Solartraveler/UniversalboxArm/src/apps/11-adc-scope/readme.md

Plots signals of the ADC inputs. Supports trigger and timebase selection.
