Solartraveler/UniversalboxArm/src/apps/10-infrared-decoder/readme.md

Decodes infrared protocols

Shows the last received infrared protocol on the LCD and serial port.

The 1. red LED shows any IR activity.
