Solartraveler/UniversalboxArm/src/apps/08-freertos-helloworld/readme.md

Simple application showing how to run FreeRTOS

Creates 4 Tasks:

1. Letting LED 1 flash

2. Control LED 2 with the input buttons

3. Periodically reset watchdog of the coprocessor

4. Waiting for input on the serial port
