Solartraveler/UniversalboxArm/src/apps/05-coprocessor-control/readme.md

Interacts with the coprocessor over SPI

Use when the AVR coprocessor is programmed with the 05-spi-with-charger firmware.

Allows checking the charging conditions
