Solartraveler/UniversalboxArm/src/apps/04-coprocessor-uart-forward/readme.md

Forwards serial data from the coprocessor

Use when the AVR coprocessor is programmed with the 02-test-everything firmware.

Data from the coprocessor are forwared to the RS232 port.
This avoids connecting a 3.3V to RS232 converter to TP20 of the PCB.

The up key generates a CPU reset.
