Solartraveler/UniversalboxArm/src/apps/01-blinky-hal/readme.md

No key: LEDs count/toggle with 4Hz.

Key control:

Left: 8Hz counting speed

Right: LEDs yellow

Up: LEDs red

Down: LED green
