Solartraveler/UniversalboxArm/src/apps/common/shared-init/stm32l452/main.h

#define KeyUp_Pin GPIO_PIN_13
#define KeyUp_GPIO_Port GPIOC
#define Extern4_Pin GPIO_PIN_0
#define Extern4_GPIO_Port GPIOC
#define Extern3_Pin GPIO_PIN_1
#define Extern3_GPIO_Port GPIOC
#define IrPower_Pin GPIO_PIN_2
#define IrPower_GPIO_Port GPIOC
#define Extern6_Pin GPIO_PIN_3
#define Extern6_GPIO_Port GPIOC
#define Extern14_Pin GPIO_PIN_0
#define Extern14_GPIO_Port GPIOA
#define Extern13_Pin GPIO_PIN_1
#define Extern13_GPIO_Port GPIOA
#define Extern12_Pin GPIO_PIN_2
#define Extern12_GPIO_Port GPIOA
#define Extern11_Pin GPIO_PIN_3
#define Extern11_GPIO_Port GPIOA
#define Extern7_Pin GPIO_PIN_4
#define Extern7_GPIO_Port GPIOA
#define Relay4_Pin GPIO_PIN_5
#define Relay4_GPIO_Port GPIOA
#define Intern4_Pin GPIO_PIN_6
#define Intern4_GPIO_Port GPIOA
#define Intern2_Pin GPIO_PIN_7
#define Intern2_GPIO_Port GPIOA
#define FlashCs_Pin GPIO_PIN_4
#define FlashCs_GPIO_Port GPIOC
#define EspPower_Pin GPIO_PIN_5
#define EspPower_GPIO_Port GPIOC
#define Intern3_Pin GPIO_PIN_0
#define Intern3_GPIO_Port GPIOB
#define Intern1_Pin GPIO_PIN_1
#define Intern1_GPIO_Port GPIOB
#define IrIn_Pin GPIO_PIN_2
#define IrIn_GPIO_Port GPIOB
#define EspRxArmTx_Pin GPIO_PIN_10
#define EspRxArmTx_GPIO_Port GPIOB
#define EspTxArmRx_Pin GPIO_PIN_11
#define EspTxArmRx_GPIO_Port GPIOB
#define Relay2_Pin GPIO_PIN_12
#define Relay2_GPIO_Port GPIOB
#define PerSpiSck_Pin GPIO_PIN_13
#define PerSpiSck_GPIO_Port GPIOB
#define PerSpiMiso_Pin GPIO_PIN_14
#define PerSpiMiso_GPIO_Port GPIOB
#define PerSpiMosi_Pin GPIO_PIN_15
#define PerSpiMosi_GPIO_Port GPIOB
#define Relay3_Pin GPIO_PIN_6
#define Relay3_GPIO_Port GPIOC
#define LcdA0_Pin GPIO_PIN_7
#define LcdA0_GPIO_Port GPIOC
#define KeyDown_Pin GPIO_PIN_8
#define KeyDown_GPIO_Port GPIOC
#define LcdCs_Pin GPIO_PIN_9
#define LcdCs_GPIO_Port GPIOC
#define LcdBacklight_Pin GPIO_PIN_8
#define LcdBacklight_GPIO_Port GPIOA
#define Relay1_Pin GPIO_PIN_9
#define Relay1_GPIO_Port GPIOA
#define PeripheralNPower_Pin GPIO_PIN_10
#define PeripheralNPower_GPIO_Port GPIOA
#define Led2Red_Pin GPIO_PIN_13
#define Led2Red_GPIO_Port GPIOA
#define Led2Green_Pin GPIO_PIN_14
#define Led2Green_GPIO_Port GPIOA
#define KeyLeft_Pin GPIO_PIN_15
#define KeyLeft_GPIO_Port GPIOA
#define AvrSpiSck_Pin GPIO_PIN_10
#define AvrSpiSck_GPIO_Port GPIOC
#define AvrSpiMiso_Pin GPIO_PIN_11
#define AvrSpiMiso_GPIO_Port GPIOC
#define AvrSpiMosi_Pin GPIO_PIN_12
#define AvrSpiMosi_GPIO_Port GPIOC
#define Led1Green_Pin GPIO_PIN_2
#define Led1Green_GPIO_Port GPIOD
#define Extern8_Pin GPIO_PIN_3
#define Extern8_GPIO_Port GPIOB
#define Extern9_Pin GPIO_PIN_4
#define Extern9_GPIO_Port GPIOB
#define Extern10_Pin GPIO_PIN_5
#define Extern10_GPIO_Port GPIOB
#define Rs232Tx_Pin GPIO_PIN_6
#define Rs232Tx_GPIO_Port GPIOB
#define Rs232Rx_Pin GPIO_PIN_7
#define Rs232Rx_GPIO_Port GPIOB
#define Led1Red_Pin GPIO_PIN_8
#define Led1Red_GPIO_Port GPIOB
#define KeyRight_Pin GPIO_PIN_9
#define KeyRight_GPIO_Port GPIOB
