Solartraveler/UniversalboxArm/src/apps/common/shared-init/main.c

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
/* Includes ------------------------------------------------------------------*/
#include "main.h"

/* USER CODE BEGIN Includes */

#include <reent.h>
#include <unistd.h>

#include "appInterface.h"
#include "boxlib/rs232debug.h"


/* USER CODE END Includes */


void SystemClock_Config(void);
/* USER CODE BEGIN 0 */

__attribute__((weak)) void AppCycle(void)
{


}

//See https://stackoverflow.com/questions/73742774/gcc-arm-none-eabi-11-3-is-not-implemented-and-will-always-fail

int _close_r(struct _reent * ptr, int fd) {
	(void)ptr;
	(void)fd;
	return -1;
}

_ssize_t _read_r(struct _reent * ptr, int fd, void *buf, size_t cnt) {
	(void)ptr;
	(void)fd;
	(void)buf;
	(void)cnt;
	return -1;
}

_ssize_t _write_r(struct _reent * ptr, int fd, const void *buf, size_t cnt) {
	(void)ptr;
	(void)fd;
	(void)buf;
	(void)cnt;
	return -1;
}

int _fstat_r(struct _reent * ptr, int fd, struct stat * pstat) {
	(void)ptr;
	(void)fd;
	(void)pstat;
	return -1;
}

off_t _lseek_r(struct _reent * ptr, int fd, off_t pos, int whence) {
	(void)ptr;
	(void)fd;
	(void)pos;
	(void)whence;
	return -1;
}

int _kill_r(struct _reent * ptr, int pid, int sig) {
	(void)ptr;
	(void)pid;
	(void)sig;
	return -1;
}

int _getpid_r(struct _reent * ptr) {
	(void)ptr;
	return -1;
}

int _stat_r(struct _reent * ptr, const char * file, struct stat * pstat) {
	(void)ptr;
	(void)file;
	(void)pstat;
	return -1;
}

int _isatty_r(struct _reent * ptr, int fd) {
	(void)ptr;
	(void)fd;
	return -1;
}

/* USER CODE END 0 */

/**
  * @brief  The application entry point.
  * @retval int
  */
int main(void)
{
  /* MCU Configuration--------------------------------------------------------*/

  /* Reset of all peripherals, Initializes the Flash interface and the Systick. */
  HAL_Init();

  /* Configure the system clock */
  SystemClock_Config();

  /* Initialize all configured peripherals */

  /* USER CODE BEGIN 2 */

  AppInit();

  /* USER CODE END 2 */

  /* Infinite loop */
  /* USER CODE BEGIN WHILE */
  while (1)
  {
    /* USER CODE END WHILE */

    /* USER CODE BEGIN 3 */
    AppCycle();
  }
  /* USER CODE END 3 */
}

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
