Solartraveler/UniversalboxArm/src/common/irmp/irmp.c

/*---------------------------------------------------------------------------------------------------------------------------------------------------
 * irmp.c - infrared multi-protocol decoder, supports several remote control protocols
 *
 * Copyright (c) 2009-2020 Frank Meyer - frank(at)fli4l.de
 *
 * Supported AVR mikrocontrollers:
 *
 * ATtiny87,  ATtiny167
 * ATtiny45,  ATtiny85
 * ATtiny44,  ATtiny84
 * ATmega8,   ATmega16,  ATmega32
 * ATmega162
 * ATmega164, ATmega324, ATmega644,  ATmega644P, ATmega1284, ATmega1284P
 * ATmega88,  ATmega88P, ATmega168,  ATmega168P, ATmega328P
 *
 * This program is free software; you can redistribute it and/or modify
 * it under the terms of the GNU General Public License as published by
 * the Free Software Foundation; either version 2 of the License, or
 * (at your option) any later version.
 *---------------------------------------------------------------------------------------------------------------------------------------------------
 */

#include "irmp.h"

#if IRMP_SUPPORT_GRUNDIG_PROTOCOL == 1 || IRMP_SUPPORT_NOKIA_PROTOCOL == 1 || IRMP_SUPPORT_IR60_PROTOCOL == 1
#  define IRMP_SUPPORT_GRUNDIG_NOKIA_IR60_PROTOCOL  1
#else
#  define IRMP_SUPPORT_GRUNDIG_NOKIA_IR60_PROTOCOL  0
#endif

#if IRMP_SUPPORT_SIEMENS_PROTOCOL == 1 || IRMP_SUPPORT_RUWIDO_PROTOCOL == 1
#  define IRMP_SUPPORT_SIEMENS_OR_RUWIDO_PROTOCOL   1
#else
#  define IRMP_SUPPORT_SIEMENS_OR_RUWIDO_PROTOCOL   0
#endif

#if IRMP_SUPPORT_RC5_PROTOCOL == 1 ||                   \
    IRMP_SUPPORT_RCII_PROTOCOL == 1 ||                  \
    IRMP_SUPPORT_S100_PROTOCOL == 1 ||                  \
    IRMP_SUPPORT_RC6_PROTOCOL == 1 ||                   \
    IRMP_SUPPORT_GRUNDIG_NOKIA_IR60_PROTOCOL == 1 ||    \
    IRMP_SUPPORT_SIEMENS_OR_RUWIDO_PROTOCOL == 1 ||     \
    IRMP_SUPPORT_IR60_PROTOCOL == 1 ||                  \
    IRMP_SUPPORT_A1TVBOX_PROTOCOL == 1 ||               \
    IRMP_SUPPORT_MERLIN_PROTOCOL == 1 ||                \
    IRMP_SUPPORT_ORTEK_PROTOCOL == 1
#  define IRMP_SUPPORT_MANCHESTER                   1
#else
#  define IRMP_SUPPORT_MANCHESTER                   0
#endif

#if IRMP_SUPPORT_NETBOX_PROTOCOL == 1
#  define IRMP_SUPPORT_SERIAL                       1
#else
#  define IRMP_SUPPORT_SERIAL                       0
#endif

#define IRMP_KEY_REPETITION_LEN                 (uint_fast16_t)(F_INTERRUPTS * 150.0e-3 + 0.5)           // autodetect key repetition within 150 msec

#define MIN_TOLERANCE_00                        1.0                           // -0%
#define MAX_TOLERANCE_00                        1.0                           // +0%

#define MIN_TOLERANCE_02                        0.98                          // -2%
#define MAX_TOLERANCE_02                        1.02                          // +2%

#define MIN_TOLERANCE_03                        0.97                          // -3%
#define MAX_TOLERANCE_03                        1.03                          // +3%

#define MIN_TOLERANCE_05                        0.95                          // -5%
#define MAX_TOLERANCE_05                        1.05                          // +5%

#define MIN_TOLERANCE_10                        0.9                           // -10%
#define MAX_TOLERANCE_10                        1.1                           // +10%

#define MIN_TOLERANCE_15                        0.85                          // -15%
#define MAX_TOLERANCE_15                        1.15                          // +15%

#define MIN_TOLERANCE_20                        0.8                           // -20%
#define MAX_TOLERANCE_20                        1.2                           // +20%

#define MIN_TOLERANCE_25                        0.75                          // -25%
#define MAX_TOLERANCE_25                        1.25                          // +25%

#define MIN_TOLERANCE_30                        0.7                           // -30%
#define MAX_TOLERANCE_30                        1.3                           // +30%

#define MIN_TOLERANCE_40                        0.6                           // -40%
#define MAX_TOLERANCE_40                        1.4                           // +40%

#define MIN_TOLERANCE_50                        0.5                           // -50%
#define MAX_TOLERANCE_50                        1.5                           // +50%

#define MIN_TOLERANCE_60                        0.4                           // -60%
#define MAX_TOLERANCE_60                        1.6                           // +60%

#define MIN_TOLERANCE_70                        0.3                           // -70%
#define MAX_TOLERANCE_70                        1.7                           // +70%

#define SIRCS_START_BIT_PULSE_LEN_MIN           ((uint_fast8_t)(F_INTERRUPTS * SIRCS_START_BIT_PULSE_TIME * MIN_TOLERANCE_10 + 0.5) - 1)
#define SIRCS_START_BIT_PULSE_LEN_MAX           ((uint_fast8_t)(F_INTERRUPTS * SIRCS_START_BIT_PULSE_TIME * MAX_TOLERANCE_10 + 0.5) + 1)
#define SIRCS_START_BIT_PAUSE_LEN_MIN           ((uint_fast8_t)(F_INTERRUPTS * SIRCS_START_BIT_PAUSE_TIME * MIN_TOLERANCE_20 + 0.5) - 1)
#if IRMP_SUPPORT_NETBOX_PROTOCOL                // only 5% to avoid conflict with NETBOX:
#  define SIRCS_START_BIT_PAUSE_LEN_MAX         ((uint_fast8_t)(F_INTERRUPTS * SIRCS_START_BIT_PAUSE_TIME * MAX_TOLERANCE_05 + 0.5))
#else                                           // only 5% + 1 to avoid conflict with RC6:
#  define SIRCS_START_BIT_PAUSE_LEN_MAX         ((uint_fast8_t)(F_INTERRUPTS * SIRCS_START_BIT_PAUSE_TIME * MAX_TOLERANCE_05 + 0.5) + 1)
#endif
#define SIRCS_1_PULSE_LEN_MIN                   ((uint_fast8_t)(F_INTERRUPTS * SIRCS_1_PULSE_TIME * MIN_TOLERANCE_10 + 0.5) - 1)
#define SIRCS_1_PULSE_LEN_MAX                   ((uint_fast8_t)(F_INTERRUPTS * SIRCS_1_PULSE_TIME * MAX_TOLERANCE_10 + 0.5) + 1)
#define SIRCS_0_PULSE_LEN_MIN                   ((uint_fast8_t)(F_INTERRUPTS * SIRCS_0_PULSE_TIME * MIN_TOLERANCE_10 + 0.5) - 1)
#define SIRCS_0_PULSE_LEN_MAX                   ((uint_fast8_t)(F_INTERRUPTS * SIRCS_0_PULSE_TIME * MAX_TOLERANCE_10 + 0.5) + 1)
#define SIRCS_PAUSE_LEN_MIN                     ((uint_fast8_t)(F_INTERRUPTS * SIRCS_PAUSE_TIME * MIN_TOLERANCE_10 + 0.5) - 1)
#define SIRCS_PAUSE_LEN_MAX                     ((uint_fast8_t)(F_INTERRUPTS * SIRCS_PAUSE_TIME * MAX_TOLERANCE_10 + 0.5) + 1)

#define NEC_START_BIT_PULSE_LEN_MIN             ((uint_fast8_t)(F_INTERRUPTS * NEC_START_BIT_PULSE_TIME * MIN_TOLERANCE_30 + 0.5) - 1)
#define NEC_START_BIT_PULSE_LEN_MAX             ((uint_fast8_t)(F_INTERRUPTS * NEC_START_BIT_PULSE_TIME * MAX_TOLERANCE_30 + 0.5) + 1)
#define NEC_START_BIT_PAUSE_LEN_MIN             ((uint_fast8_t)(F_INTERRUPTS * NEC_START_BIT_PAUSE_TIME * MIN_TOLERANCE_30 + 0.5) - 1)
#define NEC_START_BIT_PAUSE_LEN_MAX             ((uint_fast8_t)(F_INTERRUPTS * NEC_START_BIT_PAUSE_TIME * MAX_TOLERANCE_30 + 0.5) + 1)
#define NEC_REPEAT_START_BIT_PAUSE_LEN_MIN      ((uint_fast8_t)(F_INTERRUPTS * NEC_REPEAT_START_BIT_PAUSE_TIME * MIN_TOLERANCE_30 + 0.5) - 1)
#define NEC_REPEAT_START_BIT_PAUSE_LEN_MAX      ((uint_fast8_t)(F_INTERRUPTS * NEC_REPEAT_START_BIT_PAUSE_TIME * MAX_TOLERANCE_30 + 0.5) + 1)
#define NEC_PULSE_LEN_MIN                       ((uint_fast8_t)(F_INTERRUPTS * NEC_PULSE_TIME * MIN_TOLERANCE_30 + 0.5) - 1)
#define NEC_PULSE_LEN_MAX                       ((uint_fast8_t)(F_INTERRUPTS * NEC_PULSE_TIME * MAX_TOLERANCE_30 + 0.5) + 1)
#define NEC_1_PAUSE_LEN_MIN                     ((uint_fast8_t)(F_INTERRUPTS * NEC_1_PAUSE_TIME * MIN_TOLERANCE_30 + 0.5) - 1)
#define NEC_1_PAUSE_LEN_MAX                     ((uint_fast8_t)(F_INTERRUPTS * NEC_1_PAUSE_TIME * MAX_TOLERANCE_30 + 0.5) + 1)
#define NEC_0_PAUSE_LEN_MIN                     ((uint_fast8_t)(F_INTERRUPTS * NEC_0_PAUSE_TIME * MIN_TOLERANCE_30 + 0.5) - 1)
#define NEC_0_PAUSE_LEN_MAX                     ((uint_fast8_t)(F_INTERRUPTS * NEC_0_PAUSE_TIME * MAX_TOLERANCE_30 + 0.5) + 1)
// autodetect nec repetition frame within 50 msec:
// NEC seems to send the first repetition frame after 40ms, further repetition frames after 100 ms
#if 0
#define NEC_FRAME_REPEAT_PAUSE_LEN_MAX          (uint_fast16_t)(F_INTERRUPTS * NEC_FRAME_REPEAT_PAUSE_TIME * MAX_TOLERANCE_20 + 0.5)
#else
#define NEC_FRAME_REPEAT_PAUSE_LEN_MAX          (uint_fast16_t)(F_INTERRUPTS * 100.0e-3 * MAX_TOLERANCE_20 + 0.5)
#endif

#define MELINERA_0_PULSE_LEN_MIN                ((uint_fast8_t)(F_INTERRUPTS * MELINERA_0_PULSE_TIME * MIN_TOLERANCE_30 + 0.5) - 1)
#define MELINERA_0_PULSE_LEN_MAX                ((uint_fast8_t)(F_INTERRUPTS * MELINERA_0_PULSE_TIME * MAX_TOLERANCE_30 + 0.5) + 1)
#define MELINERA_0_PAUSE_LEN_MIN                ((uint_fast8_t)(F_INTERRUPTS * MELINERA_0_PAUSE_TIME * MIN_TOLERANCE_30 + 0.5) - 1)
#define MELINERA_0_PAUSE_LEN_MAX                ((uint_fast8_t)(F_INTERRUPTS * MELINERA_0_PAUSE_TIME * MAX_TOLERANCE_30 + 0.5) + 1)
#define MELINERA_1_PULSE_LEN_MIN                ((uint_fast8_t)(F_INTERRUPTS * MELINERA_1_PULSE_TIME * MIN_TOLERANCE_30 + 0.5) - 1)
#define MELINERA_1_PULSE_LEN_MAX                ((uint_fast8_t)(F_INTERRUPTS * MELINERA_1_PULSE_TIME * MAX_TOLERANCE_30 + 0.5) + 1)
#define MELINERA_1_PAUSE_LEN_MIN                ((uint_fast8_t)(F_INTERRUPTS * MELINERA_1_PAUSE_TIME * MIN_TOLERANCE_30 + 0.5) - 1)
#define MELINERA_1_PAUSE_LEN_MAX                ((uint_fast8_t)(F_INTERRUPTS * MELINERA_1_PAUSE_TIME * MAX_TOLERANCE_30 + 0.5) + 1)

#define SAMSUNG_START_BIT_PULSE_LEN_MIN         ((uint_fast8_t)(F_INTERRUPTS * SAMSUNG_START_BIT_PULSE_TIME * MIN_TOLERANCE_10 + 0.5) - 1)
#define SAMSUNG_START_BIT_PULSE_LEN_MAX         ((uint_fast8_t)(F_INTERRUPTS * SAMSUNG_START_BIT_PULSE_TIME * MAX_TOLERANCE_10 + 0.5) + 1)
#define SAMSUNG_START_BIT_PAUSE_LEN_MIN         ((uint_fast8_t)(F_INTERRUPTS * SAMSUNG_START_BIT_PAUSE_TIME * MIN_TOLERANCE_10 + 0.5) - 1)
#define SAMSUNG_START_BIT_PAUSE_LEN_MAX         ((uint_fast8_t)(F_INTERRUPTS * SAMSUNG_START_BIT_PAUSE_TIME * MAX_TOLERANCE_10 + 0.5) + 1)
#define SAMSUNG_PULSE_LEN_MIN                   ((uint_fast8_t)(F_INTERRUPTS * SAMSUNG_PULSE_TIME * MIN_TOLERANCE_30 + 0.5) - 1)
#define SAMSUNG_PULSE_LEN_MAX                   ((uint_fast8_t)(F_INTERRUPTS * SAMSUNG_PULSE_TIME * MAX_TOLERANCE_30 + 0.5) + 1)
#define SAMSUNG_1_PAUSE_LEN_MIN                 ((uint_fast8_t)(F_INTERRUPTS * SAMSUNG_1_PAUSE_TIME * MIN_TOLERANCE_30 + 0.5) - 1)
#define SAMSUNG_1_PAUSE_LEN_MAX                 ((uint_fast8_t)(F_INTERRUPTS * SAMSUNG_1_PAUSE_TIME * MAX_TOLERANCE_30 + 0.5) + 1)
#define SAMSUNG_0_PAUSE_LEN_MIN                 ((uint_fast8_t)(F_INTERRUPTS * SAMSUNG_0_PAUSE_TIME * MIN_TOLERANCE_30 + 0.5) - 1)
#define SAMSUNG_0_PAUSE_LEN_MAX                 ((uint_fast8_t)(F_INTERRUPTS * SAMSUNG_0_PAUSE_TIME * MAX_TOLERANCE_30 + 0.5) + 1)

#define SAMSUNGAH_START_BIT_PULSE_LEN_MIN       ((uint_fast8_t)(F_INTERRUPTS * SAMSUNGAH_START_BIT_PULSE_TIME * MIN_TOLERANCE_10 + 0.5) - 1)
#define SAMSUNGAH_START_BIT_PULSE_LEN_MAX       ((uint_fast8_t)(F_INTERRUPTS * SAMSUNGAH_START_BIT_PULSE_TIME * MAX_TOLERANCE_10 + 0.5) + 1)
#define SAMSUNGAH_START_BIT_PAUSE_LEN_MIN       ((uint_fast8_t)(F_INTERRUPTS * SAMSUNGAH_START_BIT_PAUSE_TIME * MIN_TOLERANCE_10 + 0.5) - 1)
#define SAMSUNGAH_START_BIT_PAUSE_LEN_MAX       ((uint_fast8_t)(F_INTERRUPTS * SAMSUNGAH_START_BIT_PAUSE_TIME * MAX_TOLERANCE_10 + 0.5) + 1)
#define SAMSUNGAH_PULSE_LEN_MIN                 ((uint_fast8_t)(F_INTERRUPTS * SAMSUNGAH_PULSE_TIME * MIN_TOLERANCE_30 + 0.5) - 1)
#define SAMSUNGAH_PULSE_LEN_MAX                 ((uint_fast8_t)(F_INTERRUPTS * SAMSUNGAH_PULSE_TIME * MAX_TOLERANCE_30 + 0.5) + 1)
#define SAMSUNGAH_1_PAUSE_LEN_MIN               ((uint_fast8_t)(F_INTERRUPTS * SAMSUNGAH_1_PAUSE_TIME * MIN_TOLERANCE_30 + 0.5) - 1)
#define SAMSUNGAH_1_PAUSE_LEN_MAX               ((uint_fast8_t)(F_INTERRUPTS * SAMSUNGAH_1_PAUSE_TIME * MAX_TOLERANCE_30 + 0.5) + 1)
#define SAMSUNGAH_0_PAUSE_LEN_MIN               ((uint_fast8_t)(F_INTERRUPTS * SAMSUNGAH_0_PAUSE_TIME * MIN_TOLERANCE_30 + 0.5) - 1)
#define SAMSUNGAH_0_PAUSE_LEN_MAX               ((uint_fast8_t)(F_INTERRUPTS * SAMSUNGAH_0_PAUSE_TIME * MAX_TOLERANCE_30 + 0.5) + 1)

#define MATSUSHITA_START_BIT_PULSE_LEN_MIN      ((uint_fast8_t)(F_INTERRUPTS * MATSUSHITA_START_BIT_PULSE_TIME * MIN_TOLERANCE_20 + 0.5) - 1)
#define MATSUSHITA_START_BIT_PULSE_LEN_MAX      ((uint_fast8_t)(F_INTERRUPTS * MATSUSHITA_START_BIT_PULSE_TIME * MAX_TOLERANCE_20 + 0.5) + 1)
#define MATSUSHITA_START_BIT_PAUSE_LEN_MIN      ((uint_fast8_t)(F_INTERRUPTS * MATSUSHITA_START_BIT_PAUSE_TIME * MIN_TOLERANCE_20 + 0.5) - 1)
#define MATSUSHITA_START_BIT_PAUSE_LEN_MAX      ((uint_fast8_t)(F_INTERRUPTS * MATSUSHITA_START_BIT_PAUSE_TIME * MAX_TOLERANCE_20 + 0.5) + 1)
#define MATSUSHITA_PULSE_LEN_MIN                ((uint_fast8_t)(F_INTERRUPTS * MATSUSHITA_PULSE_TIME * MIN_TOLERANCE_40 + 0.5) - 1)
#define MATSUSHITA_PULSE_LEN_MAX                ((uint_fast8_t)(F_INTERRUPTS * MATSUSHITA_PULSE_TIME * MAX_TOLERANCE_40 + 0.5) + 1)
#define MATSUSHITA_1_PAUSE_LEN_MIN              ((uint_fast8_t)(F_INTERRUPTS * MATSUSHITA_1_PAUSE_TIME * MIN_TOLERANCE_40 + 0.5) - 1)
#define MATSUSHITA_1_PAUSE_LEN_MAX              ((uint_fast8_t)(F_INTERRUPTS * MATSUSHITA_1_PAUSE_TIME * MAX_TOLERANCE_40 + 0.5) + 1)
#define MATSUSHITA_0_PAUSE_LEN_MIN              ((uint_fast8_t)(F_INTERRUPTS * MATSUSHITA_0_PAUSE_TIME * MIN_TOLERANCE_40 + 0.5) - 1)
#define MATSUSHITA_0_PAUSE_LEN_MAX              ((uint_fast8_t)(F_INTERRUPTS * MATSUSHITA_0_PAUSE_TIME * MAX_TOLERANCE_40 + 0.5) + 1)

#define KASEIKYO_START_BIT_PULSE_LEN_MIN        ((uint_fast8_t)(F_INTERRUPTS * KASEIKYO_START_BIT_PULSE_TIME * MIN_TOLERANCE_20 + 0.5) - 1)
#define KASEIKYO_START_BIT_PULSE_LEN_MAX        ((uint_fast8_t)(F_INTERRUPTS * KASEIKYO_START_BIT_PULSE_TIME * MAX_TOLERANCE_20 + 0.5) + 1)
#define KASEIKYO_START_BIT_PAUSE_LEN_MIN        ((uint_fast8_t)(F_INTERRUPTS * KASEIKYO_START_BIT_PAUSE_TIME * MIN_TOLERANCE_20 + 0.5) - 1)
#define KASEIKYO_START_BIT_PAUSE_LEN_MAX        ((uint_fast8_t)(F_INTERRUPTS * KASEIKYO_START_BIT_PAUSE_TIME * MAX_TOLERANCE_20 + 0.5) + 1)
#define KASEIKYO_PULSE_LEN_MIN                  ((uint_fast8_t)(F_INTERRUPTS * KASEIKYO_PULSE_TIME * MIN_TOLERANCE_40 + 0.5) - 1)
#define KASEIKYO_PULSE_LEN_MAX                  ((uint_fast8_t)(F_INTERRUPTS * KASEIKYO_PULSE_TIME * MAX_TOLERANCE_40 + 0.5) + 1)
#define KASEIKYO_1_PAUSE_LEN_MIN                ((uint_fast8_t)(F_INTERRUPTS * KASEIKYO_1_PAUSE_TIME * MIN_TOLERANCE_20 + 0.5) - 1)
#define KASEIKYO_1_PAUSE_LEN_MAX                ((uint_fast8_t)(F_INTERRUPTS * KASEIKYO_1_PAUSE_TIME * MAX_TOLERANCE_20 + 0.5) + 1)
#define KASEIKYO_0_PAUSE_LEN_MIN                ((uint_fast8_t)(F_INTERRUPTS * KASEIKYO_0_PAUSE_TIME * MIN_TOLERANCE_20 + 0.5) - 1)
#define KASEIKYO_0_PAUSE_LEN_MAX                ((uint_fast8_t)(F_INTERRUPTS * KASEIKYO_0_PAUSE_TIME * MAX_TOLERANCE_20 + 0.5) + 1)

#define MITSU_HEAVY_START_BIT_PULSE_LEN_MIN     ((uint_fast8_t)(F_INTERRUPTS * MITSU_HEAVY_START_BIT_PULSE_TIME * MIN_TOLERANCE_10 + 0.5) - 1)
#define MITSU_HEAVY_START_BIT_PULSE_LEN_MAX     ((uint_fast8_t)(F_INTERRUPTS * MITSU_HEAVY_START_BIT_PULSE_TIME * MAX_TOLERANCE_10 + 0.5) + 1)
#define MITSU_HEAVY_START_BIT_PAUSE_LEN_MIN     ((uint_fast8_t)(F_INTERRUPTS * MITSU_HEAVY_START_BIT_PAUSE_TIME * MIN_TOLERANCE_10 + 0.5) - 1)
#define MITSU_HEAVY_START_BIT_PAUSE_LEN_MAX     ((uint_fast8_t)(F_INTERRUPTS * MITSU_HEAVY_START_BIT_PAUSE_TIME * MAX_TOLERANCE_10 + 0.5) + 1)
#define MITSU_HEAVY_PULSE_LEN_MIN               ((uint_fast8_t)(F_INTERRUPTS * MITSU_HEAVY_PULSE_TIME * MIN_TOLERANCE_40 + 0.5) - 1)
#define MITSU_HEAVY_PULSE_LEN_MAX               ((uint_fast8_t)(F_INTERRUPTS * MITSU_HEAVY_PULSE_TIME * MAX_TOLERANCE_40 + 0.5) + 1)
#define MITSU_HEAVY_1_PAUSE_LEN_MIN             ((uint_fast8_t)(F_INTERRUPTS * MITSU_HEAVY_1_PAUSE_TIME * MIN_TOLERANCE_20 + 0.5) - 1)
#define MITSU_HEAVY_1_PAUSE_LEN_MAX             ((uint_fast8_t)(F_INTERRUPTS * MITSU_HEAVY_1_PAUSE_TIME * MAX_TOLERANCE_20 + 0.5) + 1)
#define MITSU_HEAVY_0_PAUSE_LEN_MIN             ((uint_fast8_t)(F_INTERRUPTS * MITSU_HEAVY_0_PAUSE_TIME * MIN_TOLERANCE_20 + 0.5) - 1)
#define MITSU_HEAVY_0_PAUSE_LEN_MAX             ((uint_fast8_t)(F_INTERRUPTS * MITSU_HEAVY_0_PAUSE_TIME * MAX_TOLERANCE_20 + 0.5) + 1)

#define VINCENT_START_BIT_PULSE_LEN_MIN         ((uint_fast8_t)(F_INTERRUPTS * VINCENT_START_BIT_PULSE_TIME * MIN_TOLERANCE_10 + 0.5) - 1)
#define VINCENT_START_BIT_PULSE_LEN_MAX         ((uint_fast8_t)(F_INTERRUPTS * VINCENT_START_BIT_PULSE_TIME * MAX_TOLERANCE_10 + 0.5) + 1)
#define VINCENT_START_BIT_PAUSE_LEN_MIN         ((uint_fast8_t)(F_INTERRUPTS * VINCENT_START_BIT_PAUSE_TIME * MIN_TOLERANCE_10 + 0.5) - 1)
#define VINCENT_START_BIT_PAUSE_LEN_MAX         ((uint_fast8_t)(F_INTERRUPTS * VINCENT_START_BIT_PAUSE_TIME * MAX_TOLERANCE_10 + 0.5) + 1)
#define VINCENT_PULSE_LEN_MIN                   ((uint_fast8_t)(F_INTERRUPTS * VINCENT_PULSE_TIME * MIN_TOLERANCE_40 + 0.5) - 1)
#define VINCENT_PULSE_LEN_MAX                   ((uint_fast8_t)(F_INTERRUPTS * VINCENT_PULSE_TIME * MAX_TOLERANCE_40 + 0.5) + 1)
#define VINCENT_1_PAUSE_LEN_MIN                 ((uint_fast8_t)(F_INTERRUPTS * VINCENT_1_PAUSE_TIME * MIN_TOLERANCE_20 + 0.5) - 1)
#define VINCENT_1_PAUSE_LEN_MAX                 ((uint_fast8_t)(F_INTERRUPTS * VINCENT_1_PAUSE_TIME * MAX_TOLERANCE_20 + 0.5) + 1)
#define VINCENT_0_PAUSE_LEN_MIN                 ((uint_fast8_t)(F_INTERRUPTS * VINCENT_0_PAUSE_TIME * MIN_TOLERANCE_20 + 0.5) - 1)
#define VINCENT_0_PAUSE_LEN_MAX                 ((uint_fast8_t)(F_INTERRUPTS * VINCENT_0_PAUSE_TIME * MAX_TOLERANCE_20 + 0.5) + 1)

#define PANASONIC_START_BIT_PULSE_LEN_MIN       ((uint_fast8_t)(F_INTERRUPTS * PANASONIC_START_BIT_PULSE_TIME * MIN_TOLERANCE_10 + 0.5) - 1)
#define PANASONIC_START_BIT_PULSE_LEN_MAX       ((uint_fast8_t)(F_INTERRUPTS * PANASONIC_START_BIT_PULSE_TIME * MAX_TOLERANCE_10 + 0.5) + 1)
#define PANASONIC_START_BIT_PAUSE_LEN_MIN       ((uint_fast8_t)(F_INTERRUPTS * PANASONIC_START_BIT_PAUSE_TIME * MIN_TOLERANCE_10 + 0.5) - 1)
#define PANASONIC_START_BIT_PAUSE_LEN_MAX       ((uint_fast8_t)(F_INTERRUPTS * PANASONIC_START_BIT_PAUSE_TIME * MAX_TOLERANCE_10 + 0.5) + 1)
#define PANASONIC_PULSE_LEN_MIN                 ((uint_fast8_t)(F_INTERRUPTS * PANASONIC_PULSE_TIME * MIN_TOLERANCE_40 + 0.5) - 1)
#define PANASONIC_PULSE_LEN_MAX                 ((uint_fast8_t)(F_INTERRUPTS * PANASONIC_PULSE_TIME * MAX_TOLERANCE_40 + 0.5) + 1)
#define PANASONIC_1_PAUSE_LEN_MIN               ((uint_fast8_t)(F_INTERRUPTS * PANASONIC_1_PAUSE_TIME * MIN_TOLERANCE_20 + 0.5) - 1)
#define PANASONIC_1_PAUSE_LEN_MAX               ((uint_fast8_t)(F_INTERRUPTS * PANASONIC_1_PAUSE_TIME * MAX_TOLERANCE_20 + 0.5) + 1)
#define PANASONIC_0_PAUSE_LEN_MIN               ((uint_fast8_t)(F_INTERRUPTS * PANASONIC_0_PAUSE_TIME * MIN_TOLERANCE_20 + 0.5) - 1)
#define PANASONIC_0_PAUSE_LEN_MAX               ((uint_fast8_t)(F_INTERRUPTS * PANASONIC_0_PAUSE_TIME * MAX_TOLERANCE_20 + 0.5) + 1)

#define RECS80_START_BIT_PULSE_LEN_MIN          ((uint_fast8_t)(F_INTERRUPTS * RECS80_START_BIT_PULSE_TIME * MIN_TOLERANCE_20 + 0.5) - 1)
#define RECS80_START_BIT_PULSE_LEN_MAX          ((uint_fast8_t)(F_INTERRUPTS * RECS80_START_BIT_PULSE_TIME * MAX_TOLERANCE_20 + 0.5) + 1)
#define RECS80_START_BIT_PAUSE_LEN_MIN          ((uint_fast8_t)(F_INTERRUPTS * RECS80_START_BIT_PAUSE_TIME * MIN_TOLERANCE_10 + 0.5) - 1)
#define RECS80_START_BIT_PAUSE_LEN_MAX          ((uint_fast8_t)(F_INTERRUPTS * RECS80_START_BIT_PAUSE_TIME * MAX_TOLERANCE_10 + 0.5) + 1)
#define RECS80_PULSE_LEN_MIN                    ((uint_fast8_t)(F_INTERRUPTS * RECS80_PULSE_TIME * MIN_TOLERANCE_20 + 0.5) - 1)
#define RECS80_PULSE_LEN_MAX                    ((uint_fast8_t)(F_INTERRUPTS * RECS80_PULSE_TIME * MAX_TOLERANCE_20 + 0.5) + 1)
#define RECS80_1_PAUSE_LEN_MIN                  ((uint_fast8_t)(F_INTERRUPTS * RECS80_1_PAUSE_TIME * MIN_TOLERANCE_10 + 0.5) - 1)
#define RECS80_1_PAUSE_LEN_MAX                  ((uint_fast8_t)(F_INTERRUPTS * RECS80_1_PAUSE_TIME * MAX_TOLERANCE_10 + 0.5) + 1)
#define RECS80_0_PAUSE_LEN_MIN                  ((uint_fast8_t)(F_INTERRUPTS * RECS80_0_PAUSE_TIME * MIN_TOLERANCE_10 + 0.5) - 1)
#define RECS80_0_PAUSE_LEN_MAX                  ((uint_fast8_t)(F_INTERRUPTS * RECS80_0_PAUSE_TIME * MAX_TOLERANCE_10 + 0.5) + 1)

#if IRMP_SUPPORT_BOSE_PROTOCOL == 1 // BOSE conflicts with RC5, so keep tolerance for RC5 minimal here:
#define RC5_START_BIT_LEN_MIN                   ((uint_fast8_t)(F_INTERRUPTS * RC5_BIT_TIME * MIN_TOLERANCE_05 + 0.5) - 1)
#define RC5_START_BIT_LEN_MAX                   ((uint_fast8_t)(F_INTERRUPTS * RC5_BIT_TIME * MAX_TOLERANCE_05 + 0.5) + 1)
#else
#define RC5_START_BIT_LEN_MIN                   ((uint_fast8_t)(F_INTERRUPTS * RC5_BIT_TIME * MIN_TOLERANCE_10 + 0.5) - 1)
#define RC5_START_BIT_LEN_MAX                   ((uint_fast8_t)(F_INTERRUPTS * RC5_BIT_TIME * MAX_TOLERANCE_10 + 0.5) + 1)
#endif

#define RC5_BIT_LEN_MIN                         ((uint_fast8_t)(F_INTERRUPTS * RC5_BIT_TIME * MIN_TOLERANCE_10 + 0.5) - 1)
#define RC5_BIT_LEN_MAX                         ((uint_fast8_t)(F_INTERRUPTS * RC5_BIT_TIME * MAX_TOLERANCE_10 + 0.5) + 1)

#define RCII_START_BIT_PULSE_LEN_MIN            ((uint_fast8_t)(F_INTERRUPTS * RCII_START_BIT_PULSE_TIME * MIN_TOLERANCE_05 + 0.5) - 1)
#define RCII_START_BIT_PULSE_LEN_MAX            ((uint_fast8_t)(F_INTERRUPTS * RCII_START_BIT_PULSE_TIME * MAX_TOLERANCE_05 + 0.5) + 1)
#define RCII_START_BIT_PAUSE_LEN_MIN            ((uint_fast8_t)(F_INTERRUPTS * RCII_START_BIT_PAUSE_TIME * MIN_TOLERANCE_05 + 0.5) - 1)
#define RCII_START_BIT_PAUSE_LEN_MAX            ((uint_fast8_t)(F_INTERRUPTS * RCII_START_BIT_PAUSE_TIME * MAX_TOLERANCE_05 + 0.5) + 1)
#define RCII_START_BIT2_PULSE_LEN_MIN           ((uint_fast8_t)(F_INTERRUPTS * RCII_START_BIT2_PULSE_TIME * MIN_TOLERANCE_05 + 0.5) - 1)
#define RCII_START_BIT2_PULSE_LEN_MAX           ((uint_fast8_t)(F_INTERRUPTS * RCII_START_BIT2_PULSE_TIME * MAX_TOLERANCE_05 + 0.5) + 1)

#define RCII_BIT_LEN_MIN                        ((uint_fast8_t)(F_INTERRUPTS * RCII_BIT_TIME * MIN_TOLERANCE_30 + 0.5) - 1)
#define RCII_BIT_LEN                            ((uint_fast8_t)(F_INTERRUPTS * RCII_BIT_TIME))
#define RCII_BIT_LEN_MAX                        ((uint_fast8_t)(F_INTERRUPTS * RCII_BIT_TIME * MAX_TOLERANCE_30 + 0.5) + 1)

#if IRMP_SUPPORT_BOSE_PROTOCOL == 1 // BOSE conflicts with S100, so keep tolerance for S100 minimal here:
#define S100_START_BIT_LEN_MIN                   ((uint_fast8_t)(F_INTERRUPTS * S100_BIT_TIME * MIN_TOLERANCE_05 + 0.5) - 1)
#define S100_START_BIT_LEN_MAX                   ((uint_fast8_t)(F_INTERRUPTS * S100_BIT_TIME * MAX_TOLERANCE_05 + 0.5) + 1)
#else
#define S100_START_BIT_LEN_MIN                   ((uint_fast8_t)(F_INTERRUPTS * S100_BIT_TIME * MIN_TOLERANCE_10 + 0.5) - 1)
#define S100_START_BIT_LEN_MAX                   ((uint_fast8_t)(F_INTERRUPTS * S100_BIT_TIME * MAX_TOLERANCE_10 + 0.5) + 1)
#endif

#define S100_BIT_LEN_MIN                         ((uint_fast8_t)(F_INTERRUPTS * S100_BIT_TIME * MIN_TOLERANCE_10 + 0.5) - 1)
#define S100_BIT_LEN_MAX                         ((uint_fast8_t)(F_INTERRUPTS * S100_BIT_TIME * MAX_TOLERANCE_10 + 0.5) + 1)

#define DENON_PULSE_LEN_MIN                     ((uint_fast8_t)(F_INTERRUPTS * DENON_PULSE_TIME * MIN_TOLERANCE_10 + 0.5) - 1)
#define DENON_PULSE_LEN_MAX                     ((uint_fast8_t)(F_INTERRUPTS * DENON_PULSE_TIME * MAX_TOLERANCE_20 + 0.5) + 1)
#define DENON_1_PAUSE_LEN_MIN                   ((uint_fast8_t)(F_INTERRUPTS * DENON_1_PAUSE_TIME * MIN_TOLERANCE_10 + 0.5) - 1)
#define DENON_1_PAUSE_LEN_MAX                   ((uint_fast8_t)(F_INTERRUPTS * DENON_1_PAUSE_TIME * MAX_TOLERANCE_10 + 0.5) + 1)
// RUWIDO (see t-home-mediareceiver-15kHz.txt) conflicts here with DENON
#define DENON_0_PAUSE_LEN_MIN                   ((uint_fast8_t)(F_INTERRUPTS * DENON_0_PAUSE_TIME * MIN_TOLERANCE_10 + 0.5) - 1)
#define DENON_0_PAUSE_LEN_MAX                   ((uint_fast8_t)(F_INTERRUPTS * DENON_0_PAUSE_TIME * MAX_TOLERANCE_10 + 0.5) + 1)
#define DENON_AUTO_REPETITION_PAUSE_LEN         ((uint_fast16_t)(F_INTERRUPTS * DENON_AUTO_REPETITION_PAUSE_TIME * MAX_TOLERANCE_10 + 0.5) + 1)

#define THOMSON_PULSE_LEN_MIN                   ((uint_fast8_t)(F_INTERRUPTS * THOMSON_PULSE_TIME * MIN_TOLERANCE_10 + 0.5) - 1)
#define THOMSON_PULSE_LEN_MAX                   ((uint_fast8_t)(F_INTERRUPTS * THOMSON_PULSE_TIME * MAX_TOLERANCE_10 + 0.5) + 1)
#define THOMSON_1_PAUSE_LEN_MIN                 ((uint_fast8_t)(F_INTERRUPTS * THOMSON_1_PAUSE_TIME * MIN_TOLERANCE_10 + 0.5) - 1)
#define THOMSON_1_PAUSE_LEN_MAX                 ((uint_fast8_t)(F_INTERRUPTS * THOMSON_1_PAUSE_TIME * MAX_TOLERANCE_10 + 0.5) + 1)
#define THOMSON_0_PAUSE_LEN_MIN                 ((uint_fast8_t)(F_INTERRUPTS * THOMSON_0_PAUSE_TIME * MIN_TOLERANCE_10 + 0.5) - 1)
#define THOMSON_0_PAUSE_LEN_MAX                 ((uint_fast8_t)(F_INTERRUPTS * THOMSON_0_PAUSE_TIME * MAX_TOLERANCE_10 + 0.5) + 1)

#define RC6_START_BIT_PULSE_LEN_MIN             ((uint_fast8_t)(F_INTERRUPTS * RC6_START_BIT_PULSE_TIME * MIN_TOLERANCE_10 + 0.5) - 1)
#define RC6_START_BIT_PULSE_LEN_MAX             ((uint_fast8_t)(F_INTERRUPTS * RC6_START_BIT_PULSE_TIME * MAX_TOLERANCE_10 + 0.5) + 1)
#define RC6_START_BIT_PAUSE_LEN_MIN             ((uint_fast8_t)(F_INTERRUPTS * RC6_START_BIT_PAUSE_TIME * MIN_TOLERANCE_10 + 0.5) - 1)
#define RC6_START_BIT_PAUSE_LEN_MAX             ((uint_fast8_t)(F_INTERRUPTS * RC6_START_BIT_PAUSE_TIME * MAX_TOLERANCE_10 + 0.5) + 1)
#define RC6_TOGGLE_BIT_LEN_MIN                  ((uint_fast8_t)(F_INTERRUPTS * RC6_TOGGLE_BIT_TIME * MIN_TOLERANCE_10 + 0.5) - 1)
#define RC6_TOGGLE_BIT_LEN_MAX                  ((uint_fast8_t)(F_INTERRUPTS * RC6_TOGGLE_BIT_TIME * MAX_TOLERANCE_10 + 0.5) + 1)
#define RC6_BIT_PULSE_LEN_MIN                   ((uint_fast8_t)(F_INTERRUPTS * RC6_BIT_TIME * MIN_TOLERANCE_10 + 0.5) - 1)
#define RC6_BIT_PULSE_LEN_MAX                   ((uint_fast8_t)(F_INTERRUPTS * RC6_BIT_TIME * MAX_TOLERANCE_60 + 0.5) + 1)       // pulses: 300 - 800
#define RC6_BIT_PAUSE_LEN_MIN                   ((uint_fast8_t)(F_INTERRUPTS * RC6_BIT_TIME * MIN_TOLERANCE_10 + 0.5) - 1)
#define RC6_BIT_PAUSE_LEN_MAX                   ((uint_fast8_t)(F_INTERRUPTS * RC6_BIT_TIME * MAX_TOLERANCE_20 + 0.5) + 1)       // pauses: 300 - 600

#define RECS80EXT_START_BIT_PULSE_LEN_MIN       ((uint_fast8_t)(F_INTERRUPTS * RECS80EXT_START_BIT_PULSE_TIME * MIN_TOLERANCE_20 + 0.5) - 1)
#define RECS80EXT_START_BIT_PULSE_LEN_MAX       ((uint_fast8_t)(F_INTERRUPTS * RECS80EXT_START_BIT_PULSE_TIME * MAX_TOLERANCE_20 + 0.5) + 1)
#define RECS80EXT_START_BIT_PAUSE_LEN_MIN       ((uint_fast8_t)(F_INTERRUPTS * RECS80EXT_START_BIT_PAUSE_TIME * MIN_TOLERANCE_10 + 0.5) - 1)
#define RECS80EXT_START_BIT_PAUSE_LEN_MAX       ((uint_fast8_t)(F_INTERRUPTS * RECS80EXT_START_BIT_PAUSE_TIME * MAX_TOLERANCE_10 + 0.5) + 1)
#define RECS80EXT_PULSE_LEN_MIN                 ((uint_fast8_t)(F_INTERRUPTS * RECS80EXT_PULSE_TIME * MIN_TOLERANCE_20 + 0.5) - 1)
#define RECS80EXT_PULSE_LEN_MAX                 ((uint_fast8_t)(F_INTERRUPTS * RECS80EXT_PULSE_TIME * MAX_TOLERANCE_20 + 0.5) + 1)
#define RECS80EXT_1_PAUSE_LEN_MIN               ((uint_fast8_t)(F_INTERRUPTS * RECS80EXT_1_PAUSE_TIME * MIN_TOLERANCE_10 + 0.5) - 1)
#define RECS80EXT_1_PAUSE_LEN_MAX               ((uint_fast8_t)(F_INTERRUPTS * RECS80EXT_1_PAUSE_TIME * MAX_TOLERANCE_10 + 0.5) + 1)
#define RECS80EXT_0_PAUSE_LEN_MIN               ((uint_fast8_t)(F_INTERRUPTS * RECS80EXT_0_PAUSE_TIME * MIN_TOLERANCE_10 + 0.5) - 1)
#define RECS80EXT_0_PAUSE_LEN_MAX               ((uint_fast8_t)(F_INTERRUPTS * RECS80EXT_0_PAUSE_TIME * MAX_TOLERANCE_10 + 0.5) + 1)

#define NUBERT_START_BIT_PULSE_LEN_MIN          ((uint_fast8_t)(F_INTERRUPTS * NUBERT_START_BIT_PULSE_TIME * MIN_TOLERANCE_20 + 0.5) - 1)
#define NUBERT_START_BIT_PULSE_LEN_MAX          ((uint_fast8_t)(F_INTERRUPTS * NUBERT_START_BIT_PULSE_TIME * MAX_TOLERANCE_20 + 0.5) + 1)
#define NUBERT_START_BIT_PAUSE_LEN_MIN          ((uint_fast8_t)(F_INTERRUPTS * NUBERT_START_BIT_PAUSE_TIME * MIN_TOLERANCE_20 + 0.5) - 1)
#define NUBERT_START_BIT_PAUSE_LEN_MAX          ((uint_fast8_t)(F_INTERRUPTS * NUBERT_START_BIT_PAUSE_TIME * MAX_TOLERANCE_20 + 0.5) + 1)
#define NUBERT_1_PULSE_LEN_MIN                  ((uint_fast8_t)(F_INTERRUPTS * NUBERT_1_PULSE_TIME * MIN_TOLERANCE_20 + 0.5) - 1)
#define NUBERT_1_PULSE_LEN_MAX                  ((uint_fast8_t)(F_INTERRUPTS * NUBERT_1_PULSE_TIME * MAX_TOLERANCE_20 + 0.5) + 1)
#define NUBERT_1_PAUSE_LEN_MIN                  ((uint_fast8_t)(F_INTERRUPTS * NUBERT_1_PAUSE_TIME * MIN_TOLERANCE_20 + 0.5) - 1)
#define NUBERT_1_PAUSE_LEN_MAX                  ((uint_fast8_t)(F_INTERRUPTS * NUBERT_1_PAUSE_TIME * MAX_TOLERANCE_20 + 0.5) + 1)
#define NUBERT_0_PULSE_LEN_MIN                  ((uint_fast8_t)(F_INTERRUPTS * NUBERT_0_PULSE_TIME * MIN_TOLERANCE_20 + 0.5) - 1)
#define NUBERT_0_PULSE_LEN_MAX                  ((uint_fast8_t)(F_INTERRUPTS * NUBERT_0_PULSE_TIME * MAX_TOLERANCE_20 + 0.5) + 1)
#define NUBERT_0_PAUSE_LEN_MIN                  ((uint_fast8_t)(F_INTERRUPTS * NUBERT_0_PAUSE_TIME * MIN_TOLERANCE_20 + 0.5) - 1)
#define NUBERT_0_PAUSE_LEN_MAX                  ((uint_fast8_t)(F_INTERRUPTS * NUBERT_0_PAUSE_TIME * MAX_TOLERANCE_20 + 0.5) + 1)

#define FAN_START_BIT_PULSE_LEN_MIN             ((uint_fast8_t)(F_INTERRUPTS * FAN_START_BIT_PULSE_TIME * MIN_TOLERANCE_20 + 0.5) - 1)
#define FAN_START_BIT_PULSE_LEN_MAX             ((uint_fast8_t)(F_INTERRUPTS * FAN_START_BIT_PULSE_TIME * MAX_TOLERANCE_20 + 0.5) + 1)
#define FAN_START_BIT_PAUSE_LEN_MIN             ((uint_fast8_t)(F_INTERRUPTS * FAN_START_BIT_PAUSE_TIME * MIN_TOLERANCE_20 + 0.5) - 1)
#define FAN_START_BIT_PAUSE_LEN_MAX             ((uint_fast8_t)(F_INTERRUPTS * FAN_START_BIT_PAUSE_TIME * MAX_TOLERANCE_20 + 0.5) + 1)
#define FAN_1_PULSE_LEN_MIN                     ((uint_fast8_t)(F_INTERRUPTS * FAN_1_PULSE_TIME * MIN_TOLERANCE_20 + 0.5) - 1)
#define FAN_1_PULSE_LEN_MAX                     ((uint_fast8_t)(F_INTERRUPTS * FAN_1_PULSE_TIME * MAX_TOLERANCE_20 + 0.5) + 1)
#define FAN_1_PAUSE_LEN_MIN                     ((uint_fast8_t)(F_INTERRUPTS * FAN_1_PAUSE_TIME * MIN_TOLERANCE_20 + 0.5) - 1)
#define FAN_1_PAUSE_LEN_MAX                     ((uint_fast8_t)(F_INTERRUPTS * FAN_1_PAUSE_TIME * MAX_TOLERANCE_20 + 0.5) + 1)
#define FAN_0_PULSE_LEN_MIN                     ((uint_fast8_t)(F_INTERRUPTS * FAN_0_PULSE_TIME * MIN_TOLERANCE_20 + 0.5) - 1)
#define FAN_0_PULSE_LEN_MAX                     ((uint_fast8_t)(F_INTERRUPTS * FAN_0_PULSE_TIME * MAX_TOLERANCE_20 + 0.5) + 1)
#define FAN_0_PAUSE_LEN_MIN                     ((uint_fast8_t)(F_INTERRUPTS * FAN_0_PAUSE_TIME * MIN_TOLERANCE_20 + 0.5) - 1)
#define FAN_0_PAUSE_LEN_MAX                     ((uint_fast8_t)(F_INTERRUPTS * FAN_0_PAUSE_TIME * MAX_TOLERANCE_20 + 0.5) + 1)

#define SPEAKER_START_BIT_PULSE_LEN_MIN         ((uint_fast8_t)(F_INTERRUPTS * SPEAKER_START_BIT_PULSE_TIME * MIN_TOLERANCE_20 + 0.5) - 1)
#define SPEAKER_START_BIT_PULSE_LEN_MAX         ((uint_fast8_t)(F_INTERRUPTS * SPEAKER_START_BIT_PULSE_TIME * MAX_TOLERANCE_20 + 0.5) + 1)
#define SPEAKER_START_BIT_PAUSE_LEN_MIN         ((uint_fast8_t)(F_INTERRUPTS * SPEAKER_START_BIT_PAUSE_TIME * MIN_TOLERANCE_20 + 0.5) - 1)
#define SPEAKER_START_BIT_PAUSE_LEN_MAX         ((uint_fast8_t)(F_INTERRUPTS * SPEAKER_START_BIT_PAUSE_TIME * MAX_TOLERANCE_20 + 0.5) + 1)
#define SPEAKER_1_PULSE_LEN_MIN                 ((uint_fast8_t)(F_INTERRUPTS * SPEAKER_1_PULSE_TIME * MIN_TOLERANCE_20 + 0.5) - 1)
#define SPEAKER_1_PULSE_LEN_MAX                 ((uint_fast8_t)(F_INTERRUPTS * SPEAKER_1_PULSE_TIME * MAX_TOLERANCE_20 + 0.5) + 1)
#define SPEAKER_1_PAUSE_LEN_MIN                 ((uint_fast8_t)(F_INTERRUPTS * SPEAKER_1_PAUSE_TIME * MIN_TOLERANCE_20 + 0.5) - 1)
#define SPEAKER_1_PAUSE_LEN_MAX                 ((uint_fast8_t)(F_INTERRUPTS * SPEAKER_1_PAUSE_TIME * MAX_TOLERANCE_20 + 0.5) + 1)
#define SPEAKER_0_PULSE_LEN_MIN                 ((uint_fast8_t)(F_INTERRUPTS * SPEAKER_0_PULSE_TIME * MIN_TOLERANCE_20 + 0.5) - 1)
#define SPEAKER_0_PULSE_LEN_MAX                 ((uint_fast8_t)(F_INTERRUPTS * SPEAKER_0_PULSE_TIME * MAX_TOLERANCE_20 + 0.5) + 1)
#define SPEAKER_0_PAUSE_LEN_MIN                 ((uint_fast8_t)(F_INTERRUPTS * SPEAKER_0_PAUSE_TIME * MIN_TOLERANCE_20 + 0.5) - 1)
#define SPEAKER_0_PAUSE_LEN_MAX                 ((uint_fast8_t)(F_INTERRUPTS * SPEAKER_0_PAUSE_TIME * MAX_TOLERANCE_20 + 0.5) + 1)

#define BANG_OLUFSEN_START_BIT1_PULSE_LEN_MIN   ((uint_fast8_t)(F_INTERRUPTS * BANG_OLUFSEN_START_BIT1_PULSE_TIME * MIN_TOLERANCE_10 + 0.5) - 1)
#define BANG_OLUFSEN_START_BIT1_PULSE_LEN_MAX   ((uint_fast8_t)(F_INTERRUPTS * BANG_OLUFSEN_START_BIT1_PULSE_TIME * MAX_TOLERANCE_10 + 0.5) + 1)
#define BANG_OLUFSEN_START_BIT1_PAUSE_LEN_MIN   ((uint_fast8_t)(F_INTERRUPTS * BANG_OLUFSEN_START_BIT1_PAUSE_TIME * MIN_TOLERANCE_10 + 0.5) - 1)
#define BANG_OLUFSEN_START_BIT1_PAUSE_LEN_MAX   ((uint_fast8_t)(F_INTERRUPTS * BANG_OLUFSEN_START_BIT1_PAUSE_TIME * MAX_TOLERANCE_10 + 0.5) + 1)
#define BANG_OLUFSEN_START_BIT2_PULSE_LEN_MIN   ((uint_fast8_t)(F_INTERRUPTS * BANG_OLUFSEN_START_BIT2_PULSE_TIME * MIN_TOLERANCE_10 + 0.5) - 1)
#define BANG_OLUFSEN_START_BIT2_PULSE_LEN_MAX   ((uint_fast8_t)(F_INTERRUPTS * BANG_OLUFSEN_START_BIT2_PULSE_TIME * MAX_TOLERANCE_10 + 0.5) + 1)
#define BANG_OLUFSEN_START_BIT2_PAUSE_LEN_MIN   ((uint_fast8_t)(F_INTERRUPTS * BANG_OLUFSEN_START_BIT2_PAUSE_TIME * MIN_TOLERANCE_10 + 0.5) - 1)
#define BANG_OLUFSEN_START_BIT2_PAUSE_LEN_MAX   ((uint_fast8_t)(F_INTERRUPTS * BANG_OLUFSEN_START_BIT2_PAUSE_TIME * MAX_TOLERANCE_10 + 0.5) + 1)
#define BANG_OLUFSEN_START_BIT3_PULSE_LEN_MIN   ((uint_fast8_t)(F_INTERRUPTS * BANG_OLUFSEN_START_BIT3_PULSE_TIME * MIN_TOLERANCE_10 + 0.5) - 1)
#define BANG_OLUFSEN_START_BIT3_PULSE_LEN_MAX   ((uint_fast8_t)(F_INTERRUPTS * BANG_OLUFSEN_START_BIT3_PULSE_TIME * MAX_TOLERANCE_10 + 0.5) + 1)
#define BANG_OLUFSEN_START_BIT3_PAUSE_LEN_MIN   ((uint_fast8_t)(F_INTERRUPTS * BANG_OLUFSEN_START_BIT3_PAUSE_TIME * MIN_TOLERANCE_10 + 0.5) - 1)
#define BANG_OLUFSEN_START_BIT3_PAUSE_LEN_MAX   ((PAUSE_LEN)(F_INTERRUPTS * BANG_OLUFSEN_START_BIT3_PAUSE_TIME * MAX_TOLERANCE_05 + 0.5) + 1) // value must be below IRMP_TIMEOUT
#define BANG_OLUFSEN_START_BIT4_PULSE_LEN_MIN   ((uint_fast8_t)(F_INTERRUPTS * BANG_OLUFSEN_START_BIT4_PULSE_TIME * MIN_TOLERANCE_10 + 0.5) - 1)
#define BANG_OLUFSEN_START_BIT4_PULSE_LEN_MAX   ((uint_fast8_t)(F_INTERRUPTS * BANG_OLUFSEN_START_BIT4_PULSE_TIME * MAX_TOLERANCE_10 + 0.5) + 1)
#define BANG_OLUFSEN_START_BIT4_PAUSE_LEN_MIN   ((uint_fast8_t)(F_INTERRUPTS * BANG_OLUFSEN_START_BIT4_PAUSE_TIME * MIN_TOLERANCE_10 + 0.5) - 1)
#define BANG_OLUFSEN_START_BIT4_PAUSE_LEN_MAX   ((uint_fast8_t)(F_INTERRUPTS * BANG_OLUFSEN_START_BIT4_PAUSE_TIME * MAX_TOLERANCE_10 + 0.5) + 1)
#define BANG_OLUFSEN_PULSE_LEN_MIN              ((uint_fast8_t)(F_INTERRUPTS * BANG_OLUFSEN_PULSE_TIME * MIN_TOLERANCE_10 + 0.5) - 1)
#define BANG_OLUFSEN_PULSE_LEN_MAX              ((uint_fast8_t)(F_INTERRUPTS * BANG_OLUFSEN_PULSE_TIME * MAX_TOLERANCE_10 + 0.5) + 1)
#define BANG_OLUFSEN_1_PAUSE_LEN_MIN            ((uint_fast8_t)(F_INTERRUPTS * BANG_OLUFSEN_1_PAUSE_TIME * MIN_TOLERANCE_10 + 0.5) - 1)
#define BANG_OLUFSEN_1_PAUSE_LEN_MAX            ((uint_fast8_t)(F_INTERRUPTS * BANG_OLUFSEN_1_PAUSE_TIME * MAX_TOLERANCE_10 + 0.5) + 1)
#define BANG_OLUFSEN_0_PAUSE_LEN_MIN            ((uint_fast8_t)(F_INTERRUPTS * BANG_OLUFSEN_0_PAUSE_TIME * MIN_TOLERANCE_10 + 0.5) - 1)
#define BANG_OLUFSEN_0_PAUSE_LEN_MAX            ((uint_fast8_t)(F_INTERRUPTS * BANG_OLUFSEN_0_PAUSE_TIME * MAX_TOLERANCE_10 + 0.5) + 1)
#define BANG_OLUFSEN_R_PAUSE_LEN_MIN            ((uint_fast8_t)(F_INTERRUPTS * BANG_OLUFSEN_R_PAUSE_TIME * MIN_TOLERANCE_10 + 0.5) - 1)
#define BANG_OLUFSEN_R_PAUSE_LEN_MAX            ((uint_fast8_t)(F_INTERRUPTS * BANG_OLUFSEN_R_PAUSE_TIME * MAX_TOLERANCE_10 + 0.5) + 1)
#define BANG_OLUFSEN_TRAILER_BIT_PAUSE_LEN_MIN  ((uint_fast8_t)(F_INTERRUPTS * BANG_OLUFSEN_TRAILER_BIT_PAUSE_TIME * MIN_TOLERANCE_10 + 0.5) - 1)
#define BANG_OLUFSEN_TRAILER_BIT_PAUSE_LEN_MAX  ((uint_fast8_t)(F_INTERRUPTS * BANG_OLUFSEN_TRAILER_BIT_PAUSE_TIME * MAX_TOLERANCE_10 + 0.5) + 1)

#define IR60_TIMEOUT_LEN                        ((uint_fast8_t)(F_INTERRUPTS * IR60_TIMEOUT_TIME * 0.5))
#define GRUNDIG_NOKIA_IR60_START_BIT_LEN_MIN    ((uint_fast8_t)(F_INTERRUPTS * GRUNDIG_NOKIA_IR60_BIT_TIME * MIN_TOLERANCE_10 + 0.5) - 1)
#define GRUNDIG_NOKIA_IR60_START_BIT_LEN_MAX    ((uint_fast8_t)(F_INTERRUPTS * GRUNDIG_NOKIA_IR60_BIT_TIME * MAX_TOLERANCE_10 + 0.5) + 1)
#define GRUNDIG_NOKIA_IR60_BIT_LEN_MIN          ((uint_fast8_t)(F_INTERRUPTS * GRUNDIG_NOKIA_IR60_BIT_TIME * MIN_TOLERANCE_10 + 0.5) - 1)
#define GRUNDIG_NOKIA_IR60_BIT_LEN_MAX          ((uint_fast8_t)(F_INTERRUPTS * GRUNDIG_NOKIA_IR60_BIT_TIME * MAX_TOLERANCE_10 + 0.5) + 1)
#define GRUNDIG_NOKIA_IR60_PRE_PAUSE_LEN_MIN    ((uint_fast8_t)(F_INTERRUPTS * GRUNDIG_NOKIA_IR60_PRE_PAUSE_TIME * MIN_TOLERANCE_20 + 0.5) + 1)
#define GRUNDIG_NOKIA_IR60_PRE_PAUSE_LEN_MAX    ((uint_fast8_t)(F_INTERRUPTS * GRUNDIG_NOKIA_IR60_PRE_PAUSE_TIME * MAX_TOLERANCE_20 + 0.5) + 1)

#define SIEMENS_OR_RUWIDO_START_BIT_PULSE_LEN_MIN       ((uint_fast8_t)(F_INTERRUPTS * SIEMENS_OR_RUWIDO_START_BIT_PULSE_TIME * MIN_TOLERANCE_00 + 0.5) - 1)
#define SIEMENS_OR_RUWIDO_START_BIT_PULSE_LEN_MAX       ((uint_fast8_t)(F_INTERRUPTS * SIEMENS_OR_RUWIDO_START_BIT_PULSE_TIME * MAX_TOLERANCE_20 + 0.5) + 1)
#define SIEMENS_OR_RUWIDO_START_BIT_PAUSE_LEN_MIN       ((uint_fast8_t)(F_INTERRUPTS * SIEMENS_OR_RUWIDO_START_BIT_PAUSE_TIME * MIN_TOLERANCE_00 + 0.5) - 1)
#define SIEMENS_OR_RUWIDO_START_BIT_PAUSE_LEN_MAX       ((uint_fast8_t)(F_INTERRUPTS * SIEMENS_OR_RUWIDO_START_BIT_PAUSE_TIME * MAX_TOLERANCE_20 + 0.5) + 1)
#define SIEMENS_OR_RUWIDO_BIT_PULSE_LEN_MIN             ((uint_fast8_t)(F_INTERRUPTS * SIEMENS_OR_RUWIDO_BIT_PULSE_TIME * MIN_TOLERANCE_00 + 0.5) - 1)
#define SIEMENS_OR_RUWIDO_BIT_PULSE_LEN_MAX             ((uint_fast8_t)(F_INTERRUPTS * SIEMENS_OR_RUWIDO_BIT_PULSE_TIME * MAX_TOLERANCE_20 + 0.5) + 1)
#define SIEMENS_OR_RUWIDO_BIT_PAUSE_LEN_MIN             ((uint_fast8_t)(F_INTERRUPTS * SIEMENS_OR_RUWIDO_BIT_PAUSE_TIME * MIN_TOLERANCE_00 + 0.5) - 1)
#define SIEMENS_OR_RUWIDO_BIT_PAUSE_LEN_MAX             ((uint_fast8_t)(F_INTERRUPTS * SIEMENS_OR_RUWIDO_BIT_PAUSE_TIME * MAX_TOLERANCE_20 + 0.5) + 1)

#define FDC_START_BIT_PULSE_LEN_MIN             ((uint_fast8_t)(F_INTERRUPTS * FDC_START_BIT_PULSE_TIME * MIN_TOLERANCE_05 + 0.5) - 1)   // 5%: avoid conflict with NETBOX
#define FDC_START_BIT_PULSE_LEN_MAX             ((uint_fast8_t)(F_INTERRUPTS * FDC_START_BIT_PULSE_TIME * MAX_TOLERANCE_05 + 0.5))
#define FDC_START_BIT_PAUSE_LEN_MIN             ((uint_fast8_t)(F_INTERRUPTS * FDC_START_BIT_PAUSE_TIME * MIN_TOLERANCE_05 + 0.5) - 1)
#define FDC_START_BIT_PAUSE_LEN_MAX             ((uint_fast8_t)(F_INTERRUPTS * FDC_START_BIT_PAUSE_TIME * MAX_TOLERANCE_05 + 0.5))
#define FDC_PULSE_LEN_MIN                       ((uint_fast8_t)(F_INTERRUPTS * FDC_PULSE_TIME * MIN_TOLERANCE_40 + 0.5) - 1)
#define FDC_PULSE_LEN_MAX                       ((uint_fast8_t)(F_INTERRUPTS * FDC_PULSE_TIME * MAX_TOLERANCE_50 + 0.5) + 1)
#define FDC_1_PAUSE_LEN_MIN                     ((uint_fast8_t)(F_INTERRUPTS * FDC_1_PAUSE_TIME * MIN_TOLERANCE_20 + 0.5) - 1)
#define FDC_1_PAUSE_LEN_MAX                     ((uint_fast8_t)(F_INTERRUPTS * FDC_1_PAUSE_TIME * MAX_TOLERANCE_20 + 0.5) + 1)
#if 0
#define FDC_0_PAUSE_LEN_MIN                     ((uint_fast8_t)(F_INTERRUPTS * FDC_0_PAUSE_TIME * MIN_TOLERANCE_40 + 0.5) - 1)   // could be negative: 255
#else
#define FDC_0_PAUSE_LEN_MIN                     (1)                                                                         // simply use 1
#endif
#define FDC_0_PAUSE_LEN_MAX                     ((uint_fast8_t)(F_INTERRUPTS * FDC_0_PAUSE_TIME * MAX_TOLERANCE_10 + 0.5) + 1)

#define RCCAR_START_BIT_PULSE_LEN_MIN           ((uint_fast8_t)(F_INTERRUPTS * RCCAR_START_BIT_PULSE_TIME * MIN_TOLERANCE_10 + 0.5) - 1)
#define RCCAR_START_BIT_PULSE_LEN_MAX           ((uint_fast8_t)(F_INTERRUPTS * RCCAR_START_BIT_PULSE_TIME * MAX_TOLERANCE_10 + 0.5) + 1)
#define RCCAR_START_BIT_PAUSE_LEN_MIN           ((uint_fast8_t)(F_INTERRUPTS * RCCAR_START_BIT_PAUSE_TIME * MIN_TOLERANCE_10 + 0.5) - 1)
#define RCCAR_START_BIT_PAUSE_LEN_MAX           ((uint_fast8_t)(F_INTERRUPTS * RCCAR_START_BIT_PAUSE_TIME * MAX_TOLERANCE_10 + 0.5) + 1)
#define RCCAR_PULSE_LEN_MIN                     ((uint_fast8_t)(F_INTERRUPTS * RCCAR_PULSE_TIME * MIN_TOLERANCE_20 + 0.5) - 1)
#define RCCAR_PULSE_LEN_MAX                     ((uint_fast8_t)(F_INTERRUPTS * RCCAR_PULSE_TIME * MAX_TOLERANCE_20 + 0.5) + 1)
#define RCCAR_1_PAUSE_LEN_MIN                   ((uint_fast8_t)(F_INTERRUPTS * RCCAR_1_PAUSE_TIME * MIN_TOLERANCE_30 + 0.5) - 1)
#define RCCAR_1_PAUSE_LEN_MAX                   ((uint_fast8_t)(F_INTERRUPTS * RCCAR_1_PAUSE_TIME * MAX_TOLERANCE_30 + 0.5) + 1)
#define RCCAR_0_PAUSE_LEN_MIN                   ((uint_fast8_t)(F_INTERRUPTS * RCCAR_0_PAUSE_TIME * MIN_TOLERANCE_30 + 0.5) - 1)
#define RCCAR_0_PAUSE_LEN_MAX                   ((uint_fast8_t)(F_INTERRUPTS * RCCAR_0_PAUSE_TIME * MAX_TOLERANCE_30 + 0.5) + 1)

#define JVC_START_BIT_PULSE_LEN_MIN             ((uint_fast8_t)(F_INTERRUPTS * JVC_START_BIT_PULSE_TIME * MIN_TOLERANCE_40 + 0.5) - 1)
#define JVC_START_BIT_PULSE_LEN_MAX             ((uint_fast8_t)(F_INTERRUPTS * JVC_START_BIT_PULSE_TIME * MAX_TOLERANCE_40 + 0.5) + 1)
#define JVC_REPEAT_START_BIT_PAUSE_LEN_MIN      ((uint_fast8_t)(F_INTERRUPTS * (JVC_FRAME_REPEAT_PAUSE_TIME - IRMP_TIMEOUT_TIME) * MIN_TOLERANCE_40 + 0.5) - 1)  // HACK!
#define JVC_REPEAT_START_BIT_PAUSE_LEN_MAX      ((uint_fast8_t)(F_INTERRUPTS * (JVC_FRAME_REPEAT_PAUSE_TIME - IRMP_TIMEOUT_TIME) * MAX_TOLERANCE_70 + 0.5) - 1)  // HACK!
#define JVC_PULSE_LEN_MIN                       ((uint_fast8_t)(F_INTERRUPTS * JVC_PULSE_TIME * MIN_TOLERANCE_40 + 0.5) - 1)
#define JVC_PULSE_LEN_MAX                       ((uint_fast8_t)(F_INTERRUPTS * JVC_PULSE_TIME * MAX_TOLERANCE_40 + 0.5) + 1)
#define JVC_1_PAUSE_LEN_MIN                     ((uint_fast8_t)(F_INTERRUPTS * JVC_1_PAUSE_TIME * MIN_TOLERANCE_40 + 0.5) - 1)
#define JVC_1_PAUSE_LEN_MAX                     ((uint_fast8_t)(F_INTERRUPTS * JVC_1_PAUSE_TIME * MAX_TOLERANCE_40 + 0.5) + 1)
#define JVC_0_PAUSE_LEN_MIN                     ((uint_fast8_t)(F_INTERRUPTS * JVC_0_PAUSE_TIME * MIN_TOLERANCE_40 + 0.5) - 1)
#define JVC_0_PAUSE_LEN_MAX                     ((uint_fast8_t)(F_INTERRUPTS * JVC_0_PAUSE_TIME * MAX_TOLERANCE_40 + 0.5) + 1)
// autodetect JVC repetition frame within 50 msec:
#define JVC_FRAME_REPEAT_PAUSE_LEN_MAX          (uint_fast16_t)(F_INTERRUPTS * JVC_FRAME_REPEAT_PAUSE_TIME * MAX_TOLERANCE_20 + 0.5)

#define NIKON_START_BIT_PULSE_LEN_MIN           ((uint_fast8_t)(F_INTERRUPTS * NIKON_START_BIT_PULSE_TIME * MIN_TOLERANCE_20 + 0.5) - 1)
#define NIKON_START_BIT_PULSE_LEN_MAX           ((uint_fast8_t)(F_INTERRUPTS * NIKON_START_BIT_PULSE_TIME * MAX_TOLERANCE_20 + 0.5) + 1)
#define NIKON_START_BIT_PAUSE_LEN_MIN           ((uint_fast16_t)(F_INTERRUPTS * NIKON_START_BIT_PAUSE_TIME * MIN_TOLERANCE_20 + 0.5) - 1)
#define NIKON_START_BIT_PAUSE_LEN_MAX           ((uint_fast16_t)(F_INTERRUPTS * NIKON_START_BIT_PAUSE_TIME * MAX_TOLERANCE_20 + 0.5) + 1)
#define NIKON_REPEAT_START_BIT_PAUSE_LEN_MIN    ((uint_fast8_t)(F_INTERRUPTS * NIKON_REPEAT_START_BIT_PAUSE_TIME * MIN_TOLERANCE_20 + 0.5) - 1)
#define NIKON_REPEAT_START_BIT_PAUSE_LEN_MAX    ((uint_fast8_t)(F_INTERRUPTS * NIKON_REPEAT_START_BIT_PAUSE_TIME * MAX_TOLERANCE_20 + 0.5) + 1)
#define NIKON_PULSE_LEN_MIN                     ((uint_fast8_t)(F_INTERRUPTS * NIKON_PULSE_TIME * MIN_TOLERANCE_20 + 0.5) - 1)
#define NIKON_PULSE_LEN_MAX                     ((uint_fast8_t)(F_INTERRUPTS * NIKON_PULSE_TIME * MAX_TOLERANCE_20 + 0.5) + 1)
#define NIKON_1_PAUSE_LEN_MIN                   ((uint_fast8_t)(F_INTERRUPTS * NIKON_1_PAUSE_TIME * MIN_TOLERANCE_20 + 0.5) - 1)
#define NIKON_1_PAUSE_LEN_MAX                   ((uint_fast8_t)(F_INTERRUPTS * NIKON_1_PAUSE_TIME * MAX_TOLERANCE_20 + 0.5) + 1)
#define NIKON_0_PAUSE_LEN_MIN                   ((uint_fast8_t)(F_INTERRUPTS * NIKON_0_PAUSE_TIME * MIN_TOLERANCE_20 + 0.5) - 1)
#define NIKON_0_PAUSE_LEN_MAX                   ((uint_fast8_t)(F_INTERRUPTS * NIKON_0_PAUSE_TIME * MAX_TOLERANCE_20 + 0.5) + 1)
#define NIKON_FRAME_REPEAT_PAUSE_LEN_MAX        (uint_fast16_t)(F_INTERRUPTS * NIKON_FRAME_REPEAT_PAUSE_TIME * MAX_TOLERANCE_20 + 0.5)

#define KATHREIN_START_BIT_PULSE_LEN_MIN        ((uint_fast8_t)(F_INTERRUPTS * KATHREIN_START_BIT_PULSE_TIME * MIN_TOLERANCE_10 + 0.5) - 1)
#define KATHREIN_START_BIT_PULSE_LEN_MAX        ((uint_fast8_t)(F_INTERRUPTS * KATHREIN_START_BIT_PULSE_TIME * MAX_TOLERANCE_10 + 0.5) + 1)
#define KATHREIN_START_BIT_PAUSE_LEN_MIN        ((uint_fast8_t)(F_INTERRUPTS * KATHREIN_START_BIT_PAUSE_TIME * MIN_TOLERANCE_10 + 0.5) - 1)
#define KATHREIN_START_BIT_PAUSE_LEN_MAX        ((uint_fast8_t)(F_INTERRUPTS * KATHREIN_START_BIT_PAUSE_TIME * MAX_TOLERANCE_10 + 0.5) + 1)
#define KATHREIN_1_PULSE_LEN_MIN                ((uint_fast8_t)(F_INTERRUPTS * KATHREIN_1_PULSE_TIME * MIN_TOLERANCE_10 + 0.5) - 1)
#define KATHREIN_1_PULSE_LEN_MAX                ((uint_fast8_t)(F_INTERRUPTS * KATHREIN_1_PULSE_TIME * MAX_TOLERANCE_10 + 0.5) + 1)
#define KATHREIN_1_PAUSE_LEN_MIN                ((uint_fast8_t)(F_INTERRUPTS * KATHREIN_1_PAUSE_TIME * MIN_TOLERANCE_10 + 0.5) - 1)
#define KATHREIN_1_PAUSE_LEN_MAX                ((uint_fast8_t)(F_INTERRUPTS * KATHREIN_1_PAUSE_TIME * MAX_TOLERANCE_10 + 0.5) + 1)
#define KATHREIN_0_PULSE_LEN_MIN                ((uint_fast8_t)(F_INTERRUPTS * KATHREIN_0_PULSE_TIME * MIN_TOLERANCE_10 + 0.5) - 1)
#define KATHREIN_0_PULSE_LEN_MAX                ((uint_fast8_t)(F_INTERRUPTS * KATHREIN_0_PULSE_TIME * MAX_TOLERANCE_10 + 0.5) + 1)
#define KATHREIN_0_PAUSE_LEN_MIN                ((uint_fast8_t)(F_INTERRUPTS * KATHREIN_0_PAUSE_TIME * MIN_TOLERANCE_10 + 0.5) - 1)
#define KATHREIN_0_PAUSE_LEN_MAX                ((uint_fast8_t)(F_INTERRUPTS * KATHREIN_0_PAUSE_TIME * MAX_TOLERANCE_10 + 0.5) + 1)
#define KATHREIN_SYNC_BIT_PAUSE_LEN_MIN         ((uint_fast8_t)(F_INTERRUPTS * KATHREIN_SYNC_BIT_PAUSE_LEN_TIME * MIN_TOLERANCE_10 + 0.5) - 1)
#define KATHREIN_SYNC_BIT_PAUSE_LEN_MAX         ((uint_fast8_t)(F_INTERRUPTS * KATHREIN_SYNC_BIT_PAUSE_LEN_TIME * MAX_TOLERANCE_10 + 0.5) + 1)

#define NETBOX_START_BIT_PULSE_LEN_MIN          ((uint_fast8_t)(F_INTERRUPTS * NETBOX_START_BIT_PULSE_TIME * MIN_TOLERANCE_10 + 0.5) - 1)
#define NETBOX_START_BIT_PULSE_LEN_MAX          ((uint_fast8_t)(F_INTERRUPTS * NETBOX_START_BIT_PULSE_TIME * MAX_TOLERANCE_10 + 0.5) + 1)
#define NETBOX_START_BIT_PAUSE_LEN_MIN          ((uint_fast8_t)(F_INTERRUPTS * NETBOX_START_BIT_PAUSE_TIME * MIN_TOLERANCE_10 + 0.5) - 1)
#define NETBOX_START_BIT_PAUSE_LEN_MAX          ((uint_fast8_t)(F_INTERRUPTS * NETBOX_START_BIT_PAUSE_TIME * MAX_TOLERANCE_10 + 0.5) + 1)
#define NETBOX_PULSE_LEN                        ((uint_fast8_t)(F_INTERRUPTS * NETBOX_PULSE_TIME))
#define NETBOX_PAUSE_LEN                        ((uint_fast8_t)(F_INTERRUPTS * NETBOX_PAUSE_TIME))
#define NETBOX_PULSE_REST_LEN                   ((uint_fast8_t)(F_INTERRUPTS * NETBOX_PULSE_TIME / 4))
#define NETBOX_PAUSE_REST_LEN                   ((uint_fast8_t)(F_INTERRUPTS * NETBOX_PAUSE_TIME / 4))

#define LEGO_START_BIT_PULSE_LEN_MIN            ((uint_fast8_t)(F_INTERRUPTS * LEGO_START_BIT_PULSE_TIME * MIN_TOLERANCE_40 + 0.5) - 1)
#define LEGO_START_BIT_PULSE_LEN_MAX            ((uint_fast8_t)(F_INTERRUPTS * LEGO_START_BIT_PULSE_TIME * MAX_TOLERANCE_40 + 0.5) + 1)
#define LEGO_START_BIT_PAUSE_LEN_MIN            ((uint_fast8_t)(F_INTERRUPTS * LEGO_START_BIT_PAUSE_TIME * MIN_TOLERANCE_40 + 0.5) - 1)
#define LEGO_START_BIT_PAUSE_LEN_MAX            ((uint_fast8_t)(F_INTERRUPTS * LEGO_START_BIT_PAUSE_TIME * MAX_TOLERANCE_40 + 0.5) + 1)
#define LEGO_PULSE_LEN_MIN                      ((uint_fast8_t)(F_INTERRUPTS * LEGO_PULSE_TIME * MIN_TOLERANCE_40 + 0.5) - 1)
#define LEGO_PULSE_LEN_MAX                      ((uint_fast8_t)(F_INTERRUPTS * LEGO_PULSE_TIME * MAX_TOLERANCE_40 + 0.5) + 1)
#define LEGO_1_PAUSE_LEN_MIN                    ((uint_fast8_t)(F_INTERRUPTS * LEGO_1_PAUSE_TIME * MIN_TOLERANCE_25 + 0.5) - 1)
#define LEGO_1_PAUSE_LEN_MAX                    ((uint_fast8_t)(F_INTERRUPTS * LEGO_1_PAUSE_TIME * MAX_TOLERANCE_40 + 0.5) + 1)
#define LEGO_0_PAUSE_LEN_MIN                    ((uint_fast8_t)(F_INTERRUPTS * LEGO_0_PAUSE_TIME * MIN_TOLERANCE_40 + 0.5) - 1)
#define LEGO_0_PAUSE_LEN_MAX                    ((uint_fast8_t)(F_INTERRUPTS * LEGO_0_PAUSE_TIME * MAX_TOLERANCE_30 + 0.5) + 1)

#define IRMP16_START_BIT_PULSE_LEN_MIN          ((uint_fast8_t)(F_INTERRUPTS * IRMP16_START_BIT_PULSE_TIME * MIN_TOLERANCE_20 + 0.5) - 1)
#define IRMP16_START_BIT_PULSE_LEN_MAX          ((uint_fast8_t)(F_INTERRUPTS * IRMP16_START_BIT_PULSE_TIME * MAX_TOLERANCE_20 + 0.5) + 1)
#define IRMP16_START_BIT_PAUSE_LEN_MIN          ((uint_fast8_t)(F_INTERRUPTS * IRMP16_START_BIT_PAUSE_TIME * MIN_TOLERANCE_20 + 0.5) - 1)
#define IRMP16_START_BIT_PAUSE_LEN_MAX          ((uint_fast8_t)(F_INTERRUPTS * IRMP16_START_BIT_PAUSE_TIME * MAX_TOLERANCE_20 + 0.5) + 1)
#define IRMP16_PULSE_LEN_MIN                    ((uint_fast8_t)(F_INTERRUPTS * IRMP16_PULSE_TIME * MIN_TOLERANCE_20 + 0.5) - 1)
#define IRMP16_PULSE_LEN_MAX                    ((uint_fast8_t)(F_INTERRUPTS * IRMP16_PULSE_TIME * MAX_TOLERANCE_20 + 0.5) + 1)
#define IRMP16_1_PAUSE_LEN_MIN                  ((uint_fast8_t)(F_INTERRUPTS * IRMP16_1_PAUSE_TIME * MIN_TOLERANCE_20 + 0.5) - 1)
#define IRMP16_1_PAUSE_LEN_MAX                  ((uint_fast8_t)(F_INTERRUPTS * IRMP16_1_PAUSE_TIME * MAX_TOLERANCE_20 + 0.5) + 1)
#define IRMP16_0_PAUSE_LEN_MIN                  ((uint_fast8_t)(F_INTERRUPTS * IRMP16_0_PAUSE_TIME * MIN_TOLERANCE_20 + 0.5) - 1)
#define IRMP16_0_PAUSE_LEN_MAX                  ((uint_fast8_t)(F_INTERRUPTS * IRMP16_0_PAUSE_TIME * MAX_TOLERANCE_20 + 0.5) + 1)

#define GREE_START_BIT_PULSE_LEN_MIN            ((uint_fast8_t)(F_INTERRUPTS * GREE_START_BIT_PULSE_TIME * MIN_TOLERANCE_20 + 0.5) - 1)
#define GREE_START_BIT_PULSE_LEN_MAX            ((uint_fast8_t)(F_INTERRUPTS * GREE_START_BIT_PULSE_TIME * MAX_TOLERANCE_20 + 0.5) + 1)
#define GREE_START_BIT_PAUSE_LEN_MIN            ((uint_fast8_t)(F_INTERRUPTS * GREE_START_BIT_PAUSE_TIME * MIN_TOLERANCE_20 + 0.5) - 1)
#define GREE_START_BIT_PAUSE_LEN_MAX            ((uint_fast8_t)(F_INTERRUPTS * GREE_START_BIT_PAUSE_TIME * MAX_TOLERANCE_20 + 0.5) + 1)
#define GREE_PULSE_LEN_MIN                      ((uint_fast8_t)(F_INTERRUPTS * GREE_PULSE_TIME * MIN_TOLERANCE_20 + 0.5) - 1)
#define GREE_PULSE_LEN_MAX                      ((uint_fast8_t)(F_INTERRUPTS * GREE_PULSE_TIME * MAX_TOLERANCE_20 + 0.5) + 1)
#define GREE_1_PAUSE_LEN_MIN                    ((uint_fast8_t)(F_INTERRUPTS * GREE_1_PAUSE_TIME * MIN_TOLERANCE_20 + 0.5) - 1)
#define GREE_1_PAUSE_LEN_MAX                    ((uint_fast8_t)(F_INTERRUPTS * GREE_1_PAUSE_TIME * MAX_TOLERANCE_20 + 0.5) + 1)
#define GREE_0_PAUSE_LEN_MIN                    ((uint_fast8_t)(F_INTERRUPTS * GREE_0_PAUSE_TIME * MIN_TOLERANCE_20 + 0.5) - 1)
#define GREE_0_PAUSE_LEN_MAX                    ((uint_fast8_t)(F_INTERRUPTS * GREE_0_PAUSE_TIME * MAX_TOLERANCE_20 + 0.5) + 1)

#define BOSE_START_BIT_PULSE_LEN_MIN             ((uint_fast8_t)(F_INTERRUPTS * BOSE_START_BIT_PULSE_TIME * MIN_TOLERANCE_30 + 0.5) - 1)
#define BOSE_START_BIT_PULSE_LEN_MAX             ((uint_fast8_t)(F_INTERRUPTS * BOSE_START_BIT_PULSE_TIME * MAX_TOLERANCE_30 + 0.5) + 1)
#define BOSE_START_BIT_PAUSE_LEN_MIN             ((uint_fast8_t)(F_INTERRUPTS * BOSE_START_BIT_PAUSE_TIME * MIN_TOLERANCE_30 + 0.5) - 1)
#define BOSE_START_BIT_PAUSE_LEN_MAX             ((uint_fast8_t)(F_INTERRUPTS * BOSE_START_BIT_PAUSE_TIME * MAX_TOLERANCE_30 + 0.5) + 1)
#define BOSE_PULSE_LEN_MIN                       ((uint_fast8_t)(F_INTERRUPTS * BOSE_PULSE_TIME * MIN_TOLERANCE_30 + 0.5) - 1)
#define BOSE_PULSE_LEN_MAX                       ((uint_fast8_t)(F_INTERRUPTS * BOSE_PULSE_TIME * MAX_TOLERANCE_30 + 0.5) + 1)
#define BOSE_1_PAUSE_LEN_MIN                     ((uint_fast8_t)(F_INTERRUPTS * BOSE_1_PAUSE_TIME * MIN_TOLERANCE_30 + 0.5) - 1)
#define BOSE_1_PAUSE_LEN_MAX                     ((uint_fast8_t)(F_INTERRUPTS * BOSE_1_PAUSE_TIME * MAX_TOLERANCE_30 + 0.5) + 1)
#define BOSE_0_PAUSE_LEN_MIN                     ((uint_fast8_t)(F_INTERRUPTS * BOSE_0_PAUSE_TIME * MIN_TOLERANCE_30 + 0.5) - 1)
#define BOSE_0_PAUSE_LEN_MAX                     ((uint_fast8_t)(F_INTERRUPTS * BOSE_0_PAUSE_TIME * MAX_TOLERANCE_30 + 0.5) + 1)
#define BOSE_FRAME_REPEAT_PAUSE_LEN_MAX          (uint_fast16_t)(F_INTERRUPTS * 100.0e-3 * MAX_TOLERANCE_20 + 0.5)

#define A1TVBOX_START_BIT_PULSE_LEN_MIN         ((uint_fast8_t)(F_INTERRUPTS * A1TVBOX_START_BIT_PULSE_TIME * MIN_TOLERANCE_10 + 0.5) - 1)
#define A1TVBOX_START_BIT_PULSE_LEN_MAX         ((uint_fast8_t)(F_INTERRUPTS * A1TVBOX_START_BIT_PULSE_TIME * MAX_TOLERANCE_10 + 0.5) + 1)
#define A1TVBOX_START_BIT_PAUSE_LEN_MIN         ((uint_fast8_t)(F_INTERRUPTS * A1TVBOX_START_BIT_PAUSE_TIME * MIN_TOLERANCE_10 + 0.5) - 1)
#define A1TVBOX_START_BIT_PAUSE_LEN_MAX         ((uint_fast8_t)(F_INTERRUPTS * A1TVBOX_START_BIT_PAUSE_TIME * MAX_TOLERANCE_10 + 0.5) + 1)
#define A1TVBOX_BIT_PULSE_LEN_MIN               ((uint_fast8_t)(F_INTERRUPTS * A1TVBOX_BIT_PULSE_TIME * MIN_TOLERANCE_30 + 0.5) - 1)
#define A1TVBOX_BIT_PULSE_LEN_MAX               ((uint_fast8_t)(F_INTERRUPTS * A1TVBOX_BIT_PULSE_TIME * MAX_TOLERANCE_30 + 0.5) + 1)
#define A1TVBOX_BIT_PAUSE_LEN_MIN               ((uint_fast8_t)(F_INTERRUPTS * A1TVBOX_BIT_PAUSE_TIME * MIN_TOLERANCE_30 + 0.5) - 1)
#define A1TVBOX_BIT_PAUSE_LEN_MAX               ((uint_fast8_t)(F_INTERRUPTS * A1TVBOX_BIT_PAUSE_TIME * MAX_TOLERANCE_30 + 0.5) + 1)

#define MERLIN_START_BIT_PULSE_LEN_MIN          ((uint_fast8_t)(F_INTERRUPTS * MERLIN_START_BIT_PULSE_TIME * MIN_TOLERANCE_10 + 0.5) - 1)
#define MERLIN_START_BIT_PULSE_LEN_MAX          ((uint_fast8_t)(F_INTERRUPTS * MERLIN_START_BIT_PULSE_TIME * MAX_TOLERANCE_10 + 0.5) + 1)
#define MERLIN_START_BIT_PAUSE_LEN_MIN          ((uint_fast8_t)(F_INTERRUPTS * MERLIN_START_BIT_PAUSE_TIME * MIN_TOLERANCE_10 + 0.5) - 1)
#define MERLIN_START_BIT_PAUSE_LEN_MAX          ((uint_fast8_t)(F_INTERRUPTS * MERLIN_START_BIT_PAUSE_TIME * MAX_TOLERANCE_10 + 0.5) + 1)
#define MERLIN_BIT_PULSE_LEN_MIN                ((uint_fast8_t)(F_INTERRUPTS * MERLIN_BIT_PULSE_TIME * MIN_TOLERANCE_30 + 0.5) - 1)
#define MERLIN_BIT_PULSE_LEN_MAX                ((uint_fast8_t)(F_INTERRUPTS * MERLIN_BIT_PULSE_TIME * MAX_TOLERANCE_30 + 0.5) + 1)
#define MERLIN_BIT_PAUSE_LEN_MIN                ((uint_fast8_t)(F_INTERRUPTS * MERLIN_BIT_PAUSE_TIME * MIN_TOLERANCE_30 + 0.5) - 1)
#define MERLIN_BIT_PAUSE_LEN_MAX                ((uint_fast8_t)(F_INTERRUPTS * MERLIN_BIT_PAUSE_TIME * MAX_TOLERANCE_30 + 0.5) + 1)

#define ORTEK_START_BIT_PULSE_LEN_MIN           ((uint_fast8_t)(F_INTERRUPTS * ORTEK_START_BIT_PULSE_TIME * MIN_TOLERANCE_10 + 0.5) - 1)
#define ORTEK_START_BIT_PULSE_LEN_MAX           ((uint_fast8_t)(F_INTERRUPTS * ORTEK_START_BIT_PULSE_TIME * MAX_TOLERANCE_10 + 0.5) + 1)
#define ORTEK_START_BIT_PAUSE_LEN_MIN           ((uint_fast8_t)(F_INTERRUPTS * ORTEK_START_BIT_PAUSE_TIME * MIN_TOLERANCE_10 + 0.5) - 1)
#define ORTEK_START_BIT_PAUSE_LEN_MAX           ((uint_fast8_t)(F_INTERRUPTS * ORTEK_START_BIT_PAUSE_TIME * MAX_TOLERANCE_10 + 0.5) + 1)
#define ORTEK_BIT_PULSE_LEN_MIN                 ((uint_fast8_t)(F_INTERRUPTS * ORTEK_BIT_TIME * MIN_TOLERANCE_10 + 0.5) - 1)
#define ORTEK_BIT_PULSE_LEN_MAX                 ((uint_fast8_t)(F_INTERRUPTS * ORTEK_BIT_TIME * MAX_TOLERANCE_10 + 0.5) + 1)
#define ORTEK_BIT_PAUSE_LEN_MIN                 ((uint_fast8_t)(F_INTERRUPTS * ORTEK_BIT_TIME * MIN_TOLERANCE_10 + 0.5) - 1)
#define ORTEK_BIT_PAUSE_LEN_MAX                 ((uint_fast8_t)(F_INTERRUPTS * ORTEK_BIT_TIME * MAX_TOLERANCE_10 + 0.5) + 1)

#define TELEFUNKEN_START_BIT_PULSE_LEN_MIN      ((uint_fast8_t)(F_INTERRUPTS * TELEFUNKEN_START_BIT_PULSE_TIME * MIN_TOLERANCE_10 + 0.5) - 1)
#define TELEFUNKEN_START_BIT_PULSE_LEN_MAX      ((uint_fast8_t)(F_INTERRUPTS * TELEFUNKEN_START_BIT_PULSE_TIME * MAX_TOLERANCE_10 + 0.5) + 1)
#define TELEFUNKEN_START_BIT_PAUSE_LEN_MIN      ((uint_fast8_t)(F_INTERRUPTS * (TELEFUNKEN_START_BIT_PAUSE_TIME) * MIN_TOLERANCE_10 + 0.5) - 1)
#define TELEFUNKEN_START_BIT_PAUSE_LEN_MAX      ((uint_fast8_t)(F_INTERRUPTS * (TELEFUNKEN_START_BIT_PAUSE_TIME) * MAX_TOLERANCE_10 + 0.5) - 1)
#define TELEFUNKEN_PULSE_LEN_MIN                ((uint_fast8_t)(F_INTERRUPTS * TELEFUNKEN_PULSE_TIME * MIN_TOLERANCE_30 + 0.5) - 1)
#define TELEFUNKEN_PULSE_LEN_MAX                ((uint_fast8_t)(F_INTERRUPTS * TELEFUNKEN_PULSE_TIME * MAX_TOLERANCE_30 + 0.5) + 1)
#define TELEFUNKEN_1_PAUSE_LEN_MIN              ((uint_fast8_t)(F_INTERRUPTS * TELEFUNKEN_1_PAUSE_TIME * MIN_TOLERANCE_30 + 0.5) - 1)
#define TELEFUNKEN_1_PAUSE_LEN_MAX              ((uint_fast8_t)(F_INTERRUPTS * TELEFUNKEN_1_PAUSE_TIME * MAX_TOLERANCE_30 + 0.5) + 1)
#define TELEFUNKEN_0_PAUSE_LEN_MIN              ((uint_fast8_t)(F_INTERRUPTS * TELEFUNKEN_0_PAUSE_TIME * MIN_TOLERANCE_30 + 0.5) - 1)
#define TELEFUNKEN_0_PAUSE_LEN_MAX              ((uint_fast8_t)(F_INTERRUPTS * TELEFUNKEN_0_PAUSE_TIME * MAX_TOLERANCE_30 + 0.5) + 1)
// autodetect TELEFUNKEN repetition frame within 50 msec:
// #define TELEFUNKEN_FRAME_REPEAT_PAUSE_LEN_MAX   (uint_fast16_t)(F_INTERRUPTS * TELEFUNKEN_FRAME_REPEAT_PAUSE_TIME * MAX_TOLERANCE_20 + 0.5)

#define ROOMBA_START_BIT_PULSE_LEN_MIN          ((uint_fast8_t)(F_INTERRUPTS * ROOMBA_START_BIT_PULSE_TIME * MIN_TOLERANCE_10 + 0.5) - 1)
#define ROOMBA_START_BIT_PULSE_LEN_MAX          ((uint_fast8_t)(F_INTERRUPTS * ROOMBA_START_BIT_PULSE_TIME * MAX_TOLERANCE_10 + 0.5) + 1)
#define ROOMBA_START_BIT_PAUSE_LEN_MIN          ((uint_fast8_t)(F_INTERRUPTS * ROOMBA_START_BIT_PAUSE_TIME * MIN_TOLERANCE_10 + 0.5) - 1)
#define ROOMBA_START_BIT_PAUSE_LEN_MAX          ((uint_fast8_t)(F_INTERRUPTS * ROOMBA_START_BIT_PAUSE_TIME * MAX_TOLERANCE_10 + 0.5) + 1)
#define ROOMBA_1_PAUSE_LEN_EXACT                ((uint_fast8_t)(F_INTERRUPTS * ROOMBA_1_PAUSE_TIME + 0.5))
#define ROOMBA_1_PULSE_LEN_MIN                  ((uint_fast8_t)(F_INTERRUPTS * ROOMBA_1_PULSE_TIME * MIN_TOLERANCE_20 + 0.5) - 1)
#define ROOMBA_1_PULSE_LEN_MAX                  ((uint_fast8_t)(F_INTERRUPTS * ROOMBA_1_PULSE_TIME * MAX_TOLERANCE_20 + 0.5) + 1)
#define ROOMBA_1_PAUSE_LEN_MIN                  ((uint_fast8_t)(F_INTERRUPTS * ROOMBA_1_PAUSE_TIME * MIN_TOLERANCE_20 + 0.5) - 1)
#define ROOMBA_1_PAUSE_LEN_MAX                  ((uint_fast8_t)(F_INTERRUPTS * ROOMBA_1_PAUSE_TIME * MAX_TOLERANCE_20 + 0.5) + 1)
#define ROOMBA_0_PAUSE_LEN                      ((uint_fast8_t)(F_INTERRUPTS * ROOMBA_0_PAUSE_TIME))
#define ROOMBA_0_PULSE_LEN_MIN                  ((uint_fast8_t)(F_INTERRUPTS * ROOMBA_0_PULSE_TIME * MIN_TOLERANCE_20 + 0.5) - 1)
#define ROOMBA_0_PULSE_LEN_MAX                  ((uint_fast8_t)(F_INTERRUPTS * ROOMBA_0_PULSE_TIME * MAX_TOLERANCE_20 + 0.5) + 1)
#define ROOMBA_0_PAUSE_LEN_MIN                  ((uint_fast8_t)(F_INTERRUPTS * ROOMBA_0_PAUSE_TIME * MIN_TOLERANCE_20 + 0.5) - 1)
#define ROOMBA_0_PAUSE_LEN_MAX                  ((uint_fast8_t)(F_INTERRUPTS * ROOMBA_0_PAUSE_TIME * MAX_TOLERANCE_20 + 0.5) + 1)

#define RCMM32_START_BIT_PULSE_LEN_MIN          ((uint_fast8_t)(F_INTERRUPTS * RCMM32_START_BIT_PULSE_TIME * MIN_TOLERANCE_05 + 0.5) - 1)
#define RCMM32_START_BIT_PULSE_LEN_MAX          ((uint_fast8_t)(F_INTERRUPTS * RCMM32_START_BIT_PULSE_TIME * MAX_TOLERANCE_05 + 0.5) + 1)
#define RCMM32_START_BIT_PAUSE_LEN_MIN          ((uint_fast8_t)(F_INTERRUPTS * RCMM32_START_BIT_PAUSE_TIME * MIN_TOLERANCE_05 + 0.5) - 1)
#define RCMM32_START_BIT_PAUSE_LEN_MAX          ((uint_fast8_t)(F_INTERRUPTS * RCMM32_START_BIT_PAUSE_TIME * MAX_TOLERANCE_05 + 0.5) + 1)
#define RCMM32_BIT_PULSE_LEN_MIN                ((uint_fast8_t)(F_INTERRUPTS * RCMM32_PULSE_TIME * MIN_TOLERANCE_05 + 0.5) - 1)
#define RCMM32_BIT_PULSE_LEN_MAX                ((uint_fast8_t)(F_INTERRUPTS * RCMM32_PULSE_TIME * MAX_TOLERANCE_05 + 0.5) + 1)
#define RCMM32_BIT_00_PAUSE_LEN_MIN             ((uint_fast8_t)(F_INTERRUPTS * RCMM32_00_PAUSE_TIME * MIN_TOLERANCE_05 + 0.5) - 1)
#define RCMM32_BIT_00_PAUSE_LEN_MAX             ((uint_fast8_t)(F_INTERRUPTS * RCMM32_00_PAUSE_TIME * MAX_TOLERANCE_05 + 0.5) + 1)
#define RCMM32_BIT_01_PAUSE_LEN_MIN             ((uint_fast8_t)(F_INTERRUPTS * RCMM32_01_PAUSE_TIME * MIN_TOLERANCE_05 + 0.5) - 1)
#define RCMM32_BIT_01_PAUSE_LEN_MAX             ((uint_fast8_t)(F_INTERRUPTS * RCMM32_01_PAUSE_TIME * MAX_TOLERANCE_05 + 0.5) + 1)
#define RCMM32_BIT_10_PAUSE_LEN_MIN             ((uint_fast8_t)(F_INTERRUPTS * RCMM32_10_PAUSE_TIME * MIN_TOLERANCE_05 + 0.5) - 1)
#define RCMM32_BIT_10_PAUSE_LEN_MAX             ((uint_fast8_t)(F_INTERRUPTS * RCMM32_10_PAUSE_TIME * MAX_TOLERANCE_05 + 0.5) + 1)
#define RCMM32_BIT_11_PAUSE_LEN_MIN             ((uint_fast8_t)(F_INTERRUPTS * RCMM32_11_PAUSE_TIME * MIN_TOLERANCE_05 + 0.5) - 1)
#define RCMM32_BIT_11_PAUSE_LEN_MAX             ((uint_fast8_t)(F_INTERRUPTS * RCMM32_11_PAUSE_TIME * MAX_TOLERANCE_05 + 0.5) + 1)

#define PENTAX_START_BIT_PULSE_LEN_MIN          ((uint_fast8_t)(F_INTERRUPTS * PENTAX_START_BIT_PULSE_TIME * MIN_TOLERANCE_10 + 0.5) - 1)
#define PENTAX_START_BIT_PULSE_LEN_MAX          ((uint_fast8_t)(F_INTERRUPTS * PENTAX_START_BIT_PULSE_TIME * MAX_TOLERANCE_10 + 0.5) + 1)
#define PENTAX_START_BIT_PAUSE_LEN_MIN          ((uint_fast8_t)(F_INTERRUPTS * PENTAX_START_BIT_PAUSE_TIME * MIN_TOLERANCE_10 + 0.5) - 1)
#define PENTAX_START_BIT_PAUSE_LEN_MAX          ((uint_fast8_t)(F_INTERRUPTS * PENTAX_START_BIT_PAUSE_TIME * MAX_TOLERANCE_10 + 0.5) + 1)
#define PENTAX_1_PAUSE_LEN_EXACT                ((uint_fast8_t)(F_INTERRUPTS * PENTAX_1_PAUSE_TIME + 0.5))
#define PENTAX_PULSE_LEN_MIN                    ((uint_fast8_t)(F_INTERRUPTS * PENTAX_PULSE_TIME * MIN_TOLERANCE_20 + 0.5) - 1)
#define PENTAX_PULSE_LEN_MAX                    ((uint_fast8_t)(F_INTERRUPTS * PENTAX_PULSE_TIME * MAX_TOLERANCE_20 + 0.5) + 1)
#define PENTAX_1_PAUSE_LEN_MIN                  ((uint_fast8_t)(F_INTERRUPTS * PENTAX_1_PAUSE_TIME * MIN_TOLERANCE_20 + 0.5) - 1)
#define PENTAX_1_PAUSE_LEN_MAX                  ((uint_fast8_t)(F_INTERRUPTS * PENTAX_1_PAUSE_TIME * MAX_TOLERANCE_20 + 0.5) + 1)
#define PENTAX_0_PAUSE_LEN                      ((uint_fast8_t)(F_INTERRUPTS * PENTAX_0_PAUSE_TIME))
#define PENTAX_PULSE_LEN_MIN                    ((uint_fast8_t)(F_INTERRUPTS * PENTAX_PULSE_TIME * MIN_TOLERANCE_20 + 0.5) - 1)
#define PENTAX_PULSE_LEN_MAX                    ((uint_fast8_t)(F_INTERRUPTS * PENTAX_PULSE_TIME * MAX_TOLERANCE_20 + 0.5) + 1)
#define PENTAX_0_PAUSE_LEN_MIN                  ((uint_fast8_t)(F_INTERRUPTS * PENTAX_0_PAUSE_TIME * MIN_TOLERANCE_20 + 0.5) - 1)
#define PENTAX_0_PAUSE_LEN_MAX                  ((uint_fast8_t)(F_INTERRUPTS * PENTAX_0_PAUSE_TIME * MAX_TOLERANCE_20 + 0.5) + 1)

#define ACP24_START_BIT_PULSE_LEN_MIN           ((uint_fast8_t)(F_INTERRUPTS * ACP24_START_BIT_PULSE_TIME * MIN_TOLERANCE_15 + 0.5) - 1)
#define ACP24_START_BIT_PULSE_LEN_MAX           ((uint_fast8_t)(F_INTERRUPTS * ACP24_START_BIT_PULSE_TIME * MAX_TOLERANCE_15 + 0.5) + 1)
#define ACP24_START_BIT_PAUSE_LEN_MIN           ((uint_fast8_t)(F_INTERRUPTS * ACP24_START_BIT_PAUSE_TIME * MIN_TOLERANCE_15 + 0.5) - 1)
#define ACP24_START_BIT_PAUSE_LEN_MAX           ((uint_fast8_t)(F_INTERRUPTS * ACP24_START_BIT_PAUSE_TIME * MAX_TOLERANCE_15 + 0.5) + 1)
#define ACP24_PULSE_LEN_MIN                     ((uint_fast8_t)(F_INTERRUPTS * ACP24_PULSE_TIME * MIN_TOLERANCE_15 + 0.5) - 1)
#define ACP24_PULSE_LEN_MAX                     ((uint_fast8_t)(F_INTERRUPTS * ACP24_PULSE_TIME * MAX_TOLERANCE_15 + 0.5) + 1)
#define ACP24_1_PAUSE_LEN_MIN                   ((uint_fast8_t)(F_INTERRUPTS * ACP24_1_PAUSE_TIME * MIN_TOLERANCE_15 + 0.5) - 1)
#define ACP24_1_PAUSE_LEN_MAX                   ((uint_fast8_t)(F_INTERRUPTS * ACP24_1_PAUSE_TIME * MAX_TOLERANCE_15 + 0.5) + 1)
#define ACP24_0_PAUSE_LEN_MIN                   ((uint_fast8_t)(F_INTERRUPTS * ACP24_0_PAUSE_TIME * MIN_TOLERANCE_15 + 0.5) - 1)
#define ACP24_0_PAUSE_LEN_MAX                   ((uint_fast8_t)(F_INTERRUPTS * ACP24_0_PAUSE_TIME * MAX_TOLERANCE_15 + 0.5) + 1)

#define METZ_START_BIT_PULSE_LEN_MIN            ((uint_fast8_t)(F_INTERRUPTS * METZ_START_BIT_PULSE_TIME * MIN_TOLERANCE_05 + 0.5) - 1)
#define METZ_START_BIT_PULSE_LEN_MAX            ((uint_fast8_t)(F_INTERRUPTS * METZ_START_BIT_PULSE_TIME * MAX_TOLERANCE_05 + 0.5) + 1)
#define METZ_START_BIT_PAUSE_LEN_MIN            ((uint_fast8_t)(F_INTERRUPTS * METZ_START_BIT_PAUSE_TIME * MIN_TOLERANCE_05 + 0.5) - 1)
#define METZ_START_BIT_PAUSE_LEN_MAX            ((uint_fast8_t)(F_INTERRUPTS * METZ_START_BIT_PAUSE_TIME * MAX_TOLERANCE_05 + 0.5) + 1)
#define METZ_PULSE_LEN_MIN                      ((uint_fast8_t)(F_INTERRUPTS * METZ_PULSE_TIME * MIN_TOLERANCE_20 + 0.5) - 1)
#define METZ_PULSE_LEN_MAX                      ((uint_fast8_t)(F_INTERRUPTS * METZ_PULSE_TIME * MAX_TOLERANCE_20 + 0.5) + 1)
#define METZ_1_PAUSE_LEN_MIN                    ((uint_fast8_t)(F_INTERRUPTS * METZ_1_PAUSE_TIME * MIN_TOLERANCE_20 + 0.5) - 1)
#define METZ_1_PAUSE_LEN_MAX                    ((uint_fast8_t)(F_INTERRUPTS * METZ_1_PAUSE_TIME * MAX_TOLERANCE_20 + 0.5) + 1)
#define METZ_0_PAUSE_LEN_MIN                    ((uint_fast8_t)(F_INTERRUPTS * METZ_0_PAUSE_TIME * MIN_TOLERANCE_20 + 0.5) - 1)
#define METZ_0_PAUSE_LEN_MAX                    ((uint_fast8_t)(F_INTERRUPTS * METZ_0_PAUSE_TIME * MAX_TOLERANCE_20 + 0.5) + 1)
#define METZ_FRAME_REPEAT_PAUSE_LEN_MAX         (uint_fast16_t)(F_INTERRUPTS * METZ_FRAME_REPEAT_PAUSE_TIME * MAX_TOLERANCE_20 + 0.5)

#define RF_GEN24_1_PAUSE_LEN_EXACT              ((uint_fast8_t)(F_INTERRUPTS * RF_GEN24_1_PAUSE_TIME + 0.5))
#define RF_GEN24_1_PULSE_LEN_MIN                ((uint_fast8_t)(F_INTERRUPTS * RF_GEN24_1_PULSE_TIME * MIN_TOLERANCE_30 + 0.5) - 1)
#define RF_GEN24_1_PULSE_LEN_MAX                ((uint_fast8_t)(F_INTERRUPTS * RF_GEN24_1_PULSE_TIME * MAX_TOLERANCE_30 + 0.5) + 1)
#define RF_GEN24_1_PAUSE_LEN_MIN                ((uint_fast8_t)(F_INTERRUPTS * RF_GEN24_1_PAUSE_TIME * MIN_TOLERANCE_30 + 0.5) - 1)
#define RF_GEN24_1_PAUSE_LEN_MAX                ((uint_fast8_t)(F_INTERRUPTS * RF_GEN24_1_PAUSE_TIME * MAX_TOLERANCE_30 + 0.5) + 1)
#define RF_GEN24_0_PAUSE_LEN                    ((uint_fast8_t)(F_INTERRUPTS * RF_GEN24_0_PAUSE_TIME))
#define RF_GEN24_0_PULSE_LEN_MIN                ((uint_fast8_t)(F_INTERRUPTS * RF_GEN24_0_PULSE_TIME * MIN_TOLERANCE_30 + 0.5) - 1)
#define RF_GEN24_0_PULSE_LEN_MAX                ((uint_fast8_t)(F_INTERRUPTS * RF_GEN24_0_PULSE_TIME * MAX_TOLERANCE_30 + 0.5) + 1)
#define RF_GEN24_0_PAUSE_LEN_MIN                ((uint_fast8_t)(F_INTERRUPTS * RF_GEN24_0_PAUSE_TIME * MIN_TOLERANCE_30 + 0.5) - 1)
#define RF_GEN24_0_PAUSE_LEN_MAX                ((uint_fast8_t)(F_INTERRUPTS * RF_GEN24_0_PAUSE_TIME * MAX_TOLERANCE_30 + 0.5) + 1)

#define RF_X10_START_BIT_PULSE_LEN_MIN          ((uint_fast8_t)(F_INTERRUPTS * RF_X10_START_BIT_PULSE_TIME * MIN_TOLERANCE_05 + 0.5) - 1)
#define RF_X10_START_BIT_PULSE_LEN_MAX          ((uint_fast8_t)(F_INTERRUPTS * RF_X10_START_BIT_PULSE_TIME * MAX_TOLERANCE_05 + 0.5) + 1)
#define RF_X10_START_BIT_PAUSE_LEN_MIN          ((uint_fast8_t)(F_INTERRUPTS * RF_X10_START_BIT_PAUSE_TIME * MIN_TOLERANCE_05 + 0.5) - 1)
#define RF_X10_START_BIT_PAUSE_LEN_MAX          ((uint_fast8_t)(F_INTERRUPTS * RF_X10_START_BIT_PAUSE_TIME * MAX_TOLERANCE_05 + 0.5) + 1)
#define RF_X10_1_PAUSE_LEN_EXACT                ((uint_fast8_t)(F_INTERRUPTS * RF_X10_1_PAUSE_TIME + 0.5))
#define RF_X10_1_PULSE_LEN_MIN                  ((uint_fast8_t)(F_INTERRUPTS * RF_X10_1_PULSE_TIME * MIN_TOLERANCE_10 + 0.5) - 1)
#define RF_X10_1_PULSE_LEN_MAX                  ((uint_fast8_t)(F_INTERRUPTS * RF_X10_1_PULSE_TIME * MAX_TOLERANCE_10 + 0.5) + 1)
#define RF_X10_1_PAUSE_LEN_MIN                  ((uint_fast8_t)(F_INTERRUPTS * RF_X10_1_PAUSE_TIME * MIN_TOLERANCE_10 + 0.5) - 1)
#define RF_X10_1_PAUSE_LEN_MAX                  ((uint_fast8_t)(F_INTERRUPTS * RF_X10_1_PAUSE_TIME * MAX_TOLERANCE_10 + 0.5) + 1)
#define RF_X10_0_PAUSE_LEN                      ((uint_fast8_t)(F_INTERRUPTS * RF_X10_0_PAUSE_TIME))
#define RF_X10_0_PULSE_LEN_MIN                  ((uint_fast8_t)(F_INTERRUPTS * RF_X10_0_PULSE_TIME * MIN_TOLERANCE_10 + 0.5) - 1)
#define RF_X10_0_PULSE_LEN_MAX                  ((uint_fast8_t)(F_INTERRUPTS * RF_X10_0_PULSE_TIME * MAX_TOLERANCE_10 + 0.5) + 1)
#define RF_X10_0_PAUSE_LEN_MIN                  ((uint_fast8_t)(F_INTERRUPTS * RF_X10_0_PAUSE_TIME * MIN_TOLERANCE_10 + 0.5) - 1)
#define RF_X10_0_PAUSE_LEN_MAX                  ((uint_fast8_t)(F_INTERRUPTS * RF_X10_0_PAUSE_TIME * MAX_TOLERANCE_10 + 0.5) + 1)

#define RF_MEDION_START_BIT_PULSE_LEN_MIN       ((uint_fast8_t)(F_INTERRUPTS * RF_MEDION_START_BIT_PULSE_TIME * MIN_TOLERANCE_05 + 0.5) - 1)
#define RF_MEDION_START_BIT_PULSE_LEN_MAX       ((uint_fast8_t)(F_INTERRUPTS * RF_MEDION_START_BIT_PULSE_TIME * MAX_TOLERANCE_05 + 0.5) + 1)
#define RF_MEDION_START_BIT_PAUSE_LEN_MIN       ((uint_fast8_t)(F_INTERRUPTS * RF_MEDION_START_BIT_PAUSE_TIME * MIN_TOLERANCE_05 + 0.5) - 1)
#define RF_MEDION_START_BIT_PAUSE_LEN_MAX       ((uint_fast8_t)(F_INTERRUPTS * RF_MEDION_START_BIT_PAUSE_TIME * MAX_TOLERANCE_05 + 0.5) + 1)
#define RF_MEDION_1_PAUSE_LEN_EXACT             ((uint_fast8_t)(F_INTERRUPTS * RF_MEDION_1_PAUSE_TIME + 0.5))
#define RF_MEDION_1_PULSE_LEN_MIN               ((uint_fast8_t)(F_INTERRUPTS * RF_MEDION_1_PULSE_TIME * MIN_TOLERANCE_10 + 0.5) - 1)
#define RF_MEDION_1_PULSE_LEN_MAX               ((uint_fast8_t)(F_INTERRUPTS * RF_MEDION_1_PULSE_TIME * MAX_TOLERANCE_10 + 0.5) + 1)
#define RF_MEDION_1_PAUSE_LEN_MIN               ((uint_fast8_t)(F_INTERRUPTS * RF_MEDION_1_PAUSE_TIME * MIN_TOLERANCE_10 + 0.5) - 1)
#define RF_MEDION_1_PAUSE_LEN_MAX               ((uint_fast8_t)(F_INTERRUPTS * RF_MEDION_1_PAUSE_TIME * MAX_TOLERANCE_10 + 0.5) + 1)
#define RF_MEDION_0_PAUSE_LEN                   ((uint_fast8_t)(F_INTERRUPTS * RF_MEDION_0_PAUSE_TIME))
#define RF_MEDION_0_PULSE_LEN_MIN               ((uint_fast8_t)(F_INTERRUPTS * RF_MEDION_0_PULSE_TIME * MIN_TOLERANCE_10 + 0.5) - 1)
#define RF_MEDION_0_PULSE_LEN_MAX               ((uint_fast8_t)(F_INTERRUPTS * RF_MEDION_0_PULSE_TIME * MAX_TOLERANCE_10 + 0.5) + 1)
#define RF_MEDION_0_PAUSE_LEN_MIN               ((uint_fast8_t)(F_INTERRUPTS * RF_MEDION_0_PAUSE_TIME * MIN_TOLERANCE_10 + 0.5) - 1)
#define RF_MEDION_0_PAUSE_LEN_MAX               ((uint_fast8_t)(F_INTERRUPTS * RF_MEDION_0_PAUSE_TIME * MAX_TOLERANCE_10 + 0.5) + 1)

#define AUTO_FRAME_REPETITION_LEN               (uint_fast16_t)(F_INTERRUPTS * AUTO_FRAME_REPETITION_TIME + 0.5)       // use uint_fast16_t!

#define STOP_BIT_PAUSE_TIME_MIN                 3000.0e-6                                                               // minimum stop bit pause time: 3.0 msec
#define STOP_BIT_PAUSE_LEN_MIN                  ((uint_fast8_t)(F_INTERRUPTS * STOP_BIT_PAUSE_TIME_MIN + 0.5) + 1)      // minimum stop bit pause len

// XC8 Compiler does not support variadic macros
#ifdef ANALYZE
#  define ANALYZE_PUTCHAR(a)                    { if (! silent)             { putchar (a);          } }
#  define ANALYZE_ONLY_NORMAL_PUTCHAR(a)        { if (! silent && !verbose) { putchar (a);          } }
// #  define ANALYZE_PRINTF(...)                { if (verbose)              { printf (__VA_ARGS__); } }
#  define ANALYZE_PRINTF1(a)                    { if (verbose)              { printf (a); } }
#  define ANALYZE_PRINTF2(a,b)                  { if (verbose)              { printf (a,b); } }
#  define ANALYZE_PRINTF3(a,b,c)                { if (verbose)              { printf (a,b,c); } }
#  define ANALYZE_PRINTF4(a,b,c,d)              { if (verbose)              { printf (a,b,c,d); } }
#  define ANALYZE_PRINTF5(a,b,c,d,e)            { if (verbose)              { printf (a,b,c,d,e); } }
#  define ANALYZE_PRINTF6(a,b,c,d,e,f)          { if (verbose)              { printf (a,b,c,d,e,f); } }
#  define ANALYZE_PRINTF7(a,b,c,d,e,f,g)        { if (verbose)              { printf (a,b,c,d,e,f,g); } }
#  define ANALYZE_PRINTF8(a,b,c,d,e,f,g,h)      { if (verbose)              { printf (a,b,c,d,e,f,g,h); } }
#  define ANALYZE_PRINTF9(a,b,c,d,e,f,g,h,i)    { if (verbose)              { printf (a,b,c,d,e,f,g,h,i); } }
//#  define ANALYZE_ONLY_NORMAL_PRINTF(...)     { if (! silent && !verbose) { printf (__VA_ARGS__); } }
#  define ANALYZE_ONLY_NORMAL_PRINTF1(a)        { if (! silent && !verbose) { printf (a); } }
#  define ANALYZE_NEWLINE()                     { if (verbose)              { putchar ('\n');       } }
static int                                      silent;
static int                                      time_counter;
static int                                      verbose;
#else
#  define ANALYZE_PUTCHAR(a)
#  define ANALYZE_ONLY_NORMAL_PUTCHAR(a)
// #  define ANALYZE_PRINTF(...)
#  define ANALYZE_PRINTF1(a)
#  define ANALYZE_PRINTF2(a,b)
#  define ANALYZE_PRINTF3(a,b,c)
#  define ANALYZE_PRINTF4(a,b,c,d)
#  define ANALYZE_PRINTF5(a,b,c,d,e)
#  define ANALYZE_PRINTF6(a,b,c,d,e,f)
#  define ANALYZE_PRINTF7(a,b,c,d,e,f,g)
#  define ANALYZE_PRINTF8(a,b,c,d,e,f,g,h)
#  define ANALYZE_PRINTF9(a,b,c,d,e,f,g,h,i)
//#  define ANALYZE_ONLY_NORMAL_PRINTF(...)
#  define ANALYZE_ONLY_NORMAL_PRINTF1(a)
#  define ANALYZE_NEWLINE()
#endif

#if IRMP_USE_CALLBACK == 1
static void                                     (*irmp_callback_ptr) (uint_fast8_t);
#endif // IRMP_USE_CALLBACK == 1

#define PARITY_CHECK_OK                         1
#define PARITY_CHECK_FAILED                     0

/*---------------------------------------------------------------------------------------------------------------------------------------------------
 *  Protocol names
 *---------------------------------------------------------------------------------------------------------------------------------------------------
 */
#if defined(UNIX_OR_WINDOWS) || IRMP_PROTOCOL_NAMES == 1
static const char proto_unknown[]       PROGMEM = "UNKNOWN";
static const char proto_sircs[]         PROGMEM = "SIRCS";
static const char proto_nec[]           PROGMEM = "NEC";
static const char proto_samsung[]       PROGMEM = "SAMSUNG";
static const char proto_matsushita[]    PROGMEM = "MATSUSH";
static const char proto_kaseikyo[]      PROGMEM = "KASEIKYO";
static const char proto_recs80[]        PROGMEM = "RECS80";
static const char proto_rc5[]           PROGMEM = "RC5";
static const char proto_denon[]         PROGMEM = "DENON";
static const char proto_rc6[]           PROGMEM = "RC6";
static const char proto_samsung32[]     PROGMEM = "SAMSG32";
static const char proto_apple[]         PROGMEM = "APPLE";
static const char proto_recs80ext[]     PROGMEM = "RECS80EX";
static const char proto_nubert[]        PROGMEM = "NUBERT";
static const char proto_bang_olufsen[]  PROGMEM = "BANG OLU";
static const char proto_grundig[]       PROGMEM = "GRUNDIG";
static const char proto_nokia[]         PROGMEM = "NOKIA";
static const char proto_siemens[]       PROGMEM = "SIEMENS";
static const char proto_fdc[]           PROGMEM = "FDC";
static const char proto_rccar[]         PROGMEM = "RCCAR";
static const char proto_jvc[]           PROGMEM = "JVC";
static const char proto_rc6a[]          PROGMEM = "RC6A";
static const char proto_nikon[]         PROGMEM = "NIKON";
static const char proto_ruwido[]        PROGMEM = "RUWIDO";
static const char proto_ir60[]          PROGMEM = "IR60";
static const char proto_kathrein[]      PROGMEM = "KATHREIN";
static const char proto_netbox[]        PROGMEM = "NETBOX";
static const char proto_nec16[]         PROGMEM = "NEC16";
static const char proto_nec42[]         PROGMEM = "NEC42";
static const char proto_lego[]          PROGMEM = "LEGO";
static const char proto_thomson[]       PROGMEM = "THOMSON";
static const char proto_bose[]          PROGMEM = "BOSE";
static const char proto_a1tvbox[]       PROGMEM = "A1TVBOX";
static const char proto_ortek[]         PROGMEM = "ORTEK";
static const char proto_telefunken[]    PROGMEM = "TELEFUNKEN";
static const char proto_roomba[]        PROGMEM = "ROOMBA";
static const char proto_rcmm32[]        PROGMEM = "RCMM32";
static const char proto_rcmm24[]        PROGMEM = "RCMM24";
static const char proto_rcmm12[]        PROGMEM = "RCMM12";
static const char proto_speaker[]       PROGMEM = "SPEAKER";
static const char proto_lgair[]         PROGMEM = "LGAIR";
static const char proto_samsung48[]     PROGMEM = "SAMSG48";
static const char proto_merlin[]        PROGMEM = "MERLIN";
static const char proto_pentax[]        PROGMEM = "PENTAX";
static const char proto_fan[]           PROGMEM = "FAN";
static const char proto_s100[]          PROGMEM = "S100";
static const char proto_acp24[]         PROGMEM = "ACP24";
static const char proto_technics[]      PROGMEM = "TECHNICS";
static const char proto_panasonic[]     PROGMEM = "PANASONIC";
static const char proto_mitsu_heavy[]   PROGMEM = "MITSU_HEAVY";
static const char proto_vincent[]       PROGMEM = "VINCENT";
static const char proto_samsungah[]     PROGMEM = "SAMSUNGAH";
static const char proto_irmp16[]        PROGMEM = "IRMP16";
static const char proto_gree[]          PROGMEM = "GREE";
static const char proto_rcii[]          PROGMEM = "RCII";
static const char proto_metz[]          PROGMEM = "METZ";
static const char proto_onkyo[]         PROGMEM = "ONKYO";

static const char proto_rf_gen24[]      PROGMEM = "RF_GEN24";
static const char proto_rf_x10[]        PROGMEM = "RF_X10";
static const char proto_rf_medion[]     PROGMEM = "RF_MEDION";
static const char proto_melinera[]      PROGMEM = "MELINERA";

const char * const
irmp_protocol_names[IRMP_N_PROTOCOLS + 1] PROGMEM =
{
    proto_unknown,
    proto_sircs,
    proto_nec,
    proto_samsung,
    proto_matsushita,
    proto_kaseikyo,
    proto_recs80,
    proto_rc5,
    proto_denon,
    proto_rc6,
    proto_samsung32,
    proto_apple,
    proto_recs80ext,
    proto_nubert,
    proto_bang_olufsen,
    proto_grundig,
    proto_nokia,
    proto_siemens,
    proto_fdc,
    proto_rccar,
    proto_jvc,
    proto_rc6a,
    proto_nikon,
    proto_ruwido,
    proto_ir60,
    proto_kathrein,
    proto_netbox,
    proto_nec16,
    proto_nec42,
    proto_lego,
    proto_thomson,
    proto_bose,
    proto_a1tvbox,
    proto_ortek,
    proto_telefunken,
    proto_roomba,
    proto_rcmm32,
    proto_rcmm24,
    proto_rcmm12,
    proto_speaker,
    proto_lgair,
    proto_samsung48,
    proto_merlin,
    proto_pentax,
    proto_fan,
    proto_s100,
    proto_acp24,
    proto_technics,
    proto_panasonic,
    proto_mitsu_heavy,
    proto_vincent,
    proto_samsungah,
    proto_irmp16,
    proto_gree,
    proto_rcii,
    proto_metz,
    proto_onkyo,

    proto_rf_gen24,
    proto_rf_x10,
    proto_rf_medion,
    proto_melinera
};

#endif

/*---------------------------------------------------------------------------------------------------------------------------------------------------
 *  Logging
 *---------------------------------------------------------------------------------------------------------------------------------------------------
 */
#if IRMP_LOGGING == 1                                                   // logging via UART

#if defined(ARM_STM32F4XX)
#  define  STM32_GPIO_CLOCK   RCC_AHB1Periph_GPIOA                      // UART2 on PA2
#  define  STM32_UART_CLOCK   RCC_APB1Periph_USART2
#  define  STM32_GPIO_PORT    GPIOA
#  define  STM32_GPIO_PIN     GPIO_Pin_2
#  define  STM32_GPIO_SOURCE  GPIO_PinSource2
#  define  STM32_UART_AF      GPIO_AF_USART2
#  define  STM32_UART_COM     USART2
#  define  STM32_UART_BAUD    115200                                    // 115200 Baud
#  include "stm32f4xx_usart.h"
#elif defined(ARM_STM32F10X)
#  define  STM32_UART_COM     USART3                                    // UART3 on PB10
#elif defined(ARDUINO)                                                  // Arduino Serial implementation
#  if defined(USB_SERIAL)
#    include "usb_serial.h"
#  else
#    error USB_SERIAL not defined in ARDUINO Environment
#  endif
#elif defined(_CHIBIOS_HAL_)                                            // ChibiOS HAL
#  if IRMP_EXT_LOGGING == 1
#    error IRMP_EXT_LOGGING not implemented for ChibiOS HAL, use regular logging instead
#  endif
#else
#  if IRMP_EXT_LOGGING == 1                                             // use external logging
#    include "irmpextlog.h"
#  else                                                                 // normal UART log (IRMP_EXT_LOGGING == 0)
#    define BAUD                                    9600L
#  ifndef UNIX_OR_WINDOWS
#    include <util/setbaud.h>
#  endif

#ifdef UBRR0H

#define UART0_UBRRH                             UBRR0H
#define UART0_UBRRL                             UBRR0L
#define UART0_UCSRA                             UCSR0A
#define UART0_UCSRB                             UCSR0B
#define UART0_UCSRC                             UCSR0C
#define UART0_UDRE_BIT_VALUE                    (1<<UDRE0)
#define UART0_UCSZ1_BIT_VALUE                   (1<<UCSZ01)
#define UART0_UCSZ0_BIT_VALUE                   (1<<UCSZ00)
#ifdef URSEL0
#define UART0_URSEL_BIT_VALUE                   (1<<URSEL0)
#else
#define UART0_URSEL_BIT_VALUE                   (0)
#endif
#define UART0_TXEN_BIT_VALUE                    (1<<TXEN0)
#define UART0_UDR                               UDR0
#define UART0_U2X                               U2X0

#else

#define UART0_UBRRH                             UBRRH
#define UART0_UBRRL                             UBRRL
#define UART0_UCSRA                             UCSRA
#define UART0_UCSRB                             UCSRB
#define UART0_UCSRC                             UCSRC
#define UART0_UDRE_BIT_VALUE                    (1<<UDRE)
#define UART0_UCSZ1_BIT_VALUE                   (1<<UCSZ1)
#define UART0_UCSZ0_BIT_VALUE                   (1<<UCSZ0)
#ifdef URSEL
#define UART0_URSEL_BIT_VALUE                   (1<<URSEL)
#else
#define UART0_URSEL_BIT_VALUE                   (0)
#endif
#define UART0_TXEN_BIT_VALUE                    (1<<TXEN)
#define UART0_UDR                               UDR
#define UART0_U2X                               U2X

#endif //UBRR0H
#endif //IRMP_EXT_LOGGING
#endif //ARM_STM32F4XX

/*---------------------------------------------------------------------------------------------------------------------------------------------------
 *  Initialize  UART
 *  @details  Initializes UART
 *---------------------------------------------------------------------------------------------------------------------------------------------------
 */
void
irmp_uart_init (void)
{
#ifndef UNIX_OR_WINDOWS
#if defined(ARM_STM32F4XX)
    GPIO_InitTypeDef GPIO_InitStructure;
    USART_InitTypeDef USART_InitStructure;

    // Clock enable vom TX Pin
    RCC_AHB1PeriphClockCmd(STM32_GPIO_CLOCK, ENABLE);

    // Clock enable der UART
    RCC_APB1PeriphClockCmd(STM32_UART_CLOCK, ENABLE);

    // UART Alternative-Funktion mit dem IO-Pin verbinden
    GPIO_PinAFConfig(STM32_GPIO_PORT,STM32_GPIO_SOURCE,STM32_UART_AF);

    // UART als Alternative-Funktion mit PushPull
    GPIO_InitStructure.GPIO_Mode = GPIO_Mode_AF;
    GPIO_InitStructure.GPIO_Speed = GPIO_Speed_100MHz;
    GPIO_InitStructure.GPIO_OType = GPIO_OType_PP;
    GPIO_InitStructure.GPIO_PuPd = GPIO_PuPd_UP;

    // TX-Pin
    GPIO_InitStructure.GPIO_Pin = STM32_GPIO_PIN;
    GPIO_Init(STM32_GPIO_PORT, &GPIO_InitStructure);

    // Oversampling
    USART_OverSampling8Cmd(STM32_UART_COM, ENABLE);

    // init baud rate, 8 data bits, 1 stop bit, no parity, no RTS+CTS
    USART_InitStructure.USART_BaudRate = STM32_UART_BAUD;
    USART_InitStructure.USART_WordLength = USART_WordLength_8b;
    USART_InitStructure.USART_StopBits = USART_StopBits_1;
    USART_InitStructure.USART_Parity = USART_Parity_No;
    USART_InitStructure.USART_HardwareFlowControl = USART_HardwareFlowControl_None;
    USART_InitStructure.USART_Mode = USART_Mode_Tx;
    USART_Init(STM32_UART_COM, &USART_InitStructure);

    // UART enable
    USART_Cmd(STM32_UART_COM, ENABLE);

#elif defined(ARM_STM32F10X)
    GPIO_InitTypeDef GPIO_InitStructure;
    USART_InitTypeDef USART_InitStructure;

    // Clock enable vom TX Pin
    RCC_APB2PeriphClockCmd(RCC_APB2Periph_GPIOB, ENABLE); // UART3 an PB10

    // Clock enable der UART
    RCC_APB1PeriphClockCmd(RCC_APB1Periph_USART3, ENABLE);

    // UART als Alternative-Funktion mit PushPull
    GPIO_InitStructure.GPIO_Mode = GPIO_Mode_AF_PP;
    GPIO_InitStructure.GPIO_Speed = GPIO_Speed_50MHz;

    // TX-Pin
    GPIO_InitStructure.GPIO_Pin = GPIO_Pin_10;
    GPIO_Init(GPIOB, &GPIO_InitStructure);

    // Oversampling
    USART_OverSampling8Cmd(STM32_UART_COM, ENABLE);

    // init baud rate, 8 data bits, 1 stop bit, no parity, no RTS+CTS
    USART_InitStructure.USART_BaudRate = 115200;
    USART_InitStructure.USART_WordLength = USART_WordLength_8b;
    USART_InitStructure.USART_StopBits = USART_StopBits_1;
    USART_InitStructure.USART_Parity = USART_Parity_No;
    USART_InitStructure.USART_HardwareFlowControl = USART_HardwareFlowControl_None;
    USART_InitStructure.USART_Mode = USART_Mode_Tx;
    USART_Init(STM32_UART_COM, &USART_InitStructure);

    // UART enable
    USART_Cmd(STM32_UART_COM, ENABLE);

#elif defined(ARDUINO)
    // we use the Arduino Serial Imlementation
    // you have to call Serial.begin(SER_BAUD); in Arduino setup() function

#elif defined (__AVR_XMEGA__)

    PMIC.CTRL |= PMIC_HILVLEN_bm;

    USARTC1.BAUDCTRLB = 0;
    USARTC1.BAUDCTRLA = F_CPU / 153600 - 1;
    USARTC1.CTRLA = USART_RXCINTLVL_HI_gc;                                                          // high INT level (receive)
    USARTC1.CTRLB = USART_TXEN_bm | USART_RXEN_bm;                                                  // activated RX and TX
    USARTC1.CTRLC = USART_CHSIZE_8BIT_gc;                                                           // 8 Bit
    PORTC.DIR |= (1<<7);                                                                            // TXD is output
    PORTC.DIR &= ~(1<<6);

#elif defined (_CHIBIOS_HAL_)
    // we use the SD interface for logging, no need to init that here

#else

#if (IRMP_EXT_LOGGING == 0)                                                                         // use UART
    UART0_UBRRH = UBRRH_VALUE;                                                                      // set baud rate
    UART0_UBRRL = UBRRL_VALUE;

#if USE_2X
    UART0_UCSRA |= (1<<UART0_U2X);
#else
    UART0_UCSRA &= ~(1<<UART0_U2X);
#endif

    UART0_UCSRC = UART0_UCSZ1_BIT_VALUE | UART0_UCSZ0_BIT_VALUE | UART0_URSEL_BIT_VALUE;
    UART0_UCSRB |= UART0_TXEN_BIT_VALUE;                                                            // enable UART TX
#else                                                                                               // other log method
    initextlog();
#endif //IRMP_EXT_LOGGING
#endif //ARM_STM32F4XX
#endif // UNIX_OR_WINDOWS
}

/*---------------------------------------------------------------------------------------------------------------------------------------------------
 *  Send character
 *  @details  Sends character
 *  @param    ch character to be transmitted
 *---------------------------------------------------------------------------------------------------------------------------------------------------
 */
void
irmp_uart_putc (unsigned char ch)
{
#ifndef UNIX_OR_WINDOWS
#if defined(ARM_STM32F4XX) || defined(ARM_STM32F10X)
    // warten bis altes Byte gesendet wurde
    while (USART_GetFlagStatus(STM32_UART_COM, USART_FLAG_TXE) == RESET)
    {
        ;
    }

    USART_SendData(STM32_UART_COM, ch);

    if (ch == '\n')
    {
        while (USART_GetFlagStatus(STM32_UART_COM, USART_FLAG_TXE) == RESET);
        USART_SendData(STM32_UART_COM, '\r');
    }

#elif defined(ARDUINO)
    // we use the Arduino Serial Imlementation
    usb_serial_putchar(ch);

#elif defined(_CHIBIOS_HAL_)
    // use the SD interface from HAL, log to IRMP_LOGGING_SD which is defined in irmpconfig.h
    sdWriteI(&IRMP_LOGGING_SD,&ch,1);      // we are called from interrupt context, so use the ...I version of the function

#else
#if (IRMP_EXT_LOGGING == 0)

#  if defined (__AVR_XMEGA__)
    while (!(USARTC1.STATUS & USART_DREIF_bm))
    {
        ;
    }

    USARTC1.DATA = ch;

#  else // AVR_MEGA
    while (!(UART0_UCSRA & UART0_UDRE_BIT_VALUE))
    {
        ;
    }

    UART0_UDR = ch;

#  endif // __AVR_XMEGA__

#else

    sendextlog(ch);                                                         // use external log

#endif // IRMP_EXT_LOGGING
#endif // ARM_STM32F4XX
#else
    fputc (ch, stderr);
#endif // UNIX_OR_WINDOWS
}

/*---------------------------------------------------------------------------------------------------------------------------------------------------
 *  Log IR signal
 *---------------------------------------------------------------------------------------------------------------------------------------------------
 */

#define STARTCYCLES                       2                                 // min count of zeros before start of logging
#define ENDBITS                        1000                                 // number of sequenced highbits to detect end
#define DATALEN                         700                                 // log buffer size

static void
irmp_log (uint_fast8_t val)
{
    static uint8_t          buf[DATALEN];                                   // logging buffer
    static uint_fast16_t    buf_idx;                                        // index
    static uint_fast8_t     startcycles;                                    // current number of start-zeros
    static uint_fast16_t    cnt;                                            // counts sequenced highbits - to detect end
    static uint_fast8_t     last_val = 1;

    if (! val && (startcycles < STARTCYCLES) && !buf_idx)                   // prevent that single random zeros init logging
    {
        startcycles++;
    }
    else
    {
        startcycles = 0;

        if (! val || buf_idx != 0)                                          // start or continue logging on "0", "1" cannot init logging
        {
            if (last_val == val)
            {
                cnt++;

                if (val && cnt > ENDBITS)                                   // if high received then look at log-stop condition
                {                                                           // if stop condition is true, output on uart
                    uint_fast8_t     i8;
                    uint_fast16_t    i;
                    uint_fast16_t    j;
                    uint_fast8_t     v = '1';
                    uint_fast16_t    d;

                    for (i8 = 0; i8 < STARTCYCLES; i8++)
                    {
                        irmp_uart_putc ('0');                               // the ignored starting zeros
                    }

                    for (i = 0; i < buf_idx; i++)
                    {
                        d = buf[i];

                        if (d == 0xff)
                        {
                            i++;
                            d = buf[i];
                            i++;
                            d |= ((uint_fast16_t) buf[i] << 8);
                        }

                        for (j = 0; j < d; j++)
                        {
                            irmp_uart_putc (v);
                        }

                        v = (v == '1') ? '0' : '1';
                    }

                    for (i8 = 0; i8 < 20; i8++)
                    {
                        irmp_uart_putc ('1');
                    }

                    irmp_uart_putc ('\n');
                    buf_idx = 0;
                    last_val = 1;
                    cnt = 0;
                }
            }
            else if (buf_idx < DATALEN - 3)
            {
                if (cnt >= 0xff)
                {
                    buf[buf_idx++]  = 0xff;
                    buf[buf_idx++]  = (cnt & 0xff);
                    buf[buf_idx]    = (cnt >> 8);
                }
                else
                {
                    buf[buf_idx] = cnt;
                }

                buf_idx++;
                cnt = 1;
                last_val = val;
            }
        }
    }
}

#else
#define irmp_log(val)
#endif //IRMP_LOGGING

typedef struct
{
    uint_fast8_t    protocol;                                                // ir protocol
    uint_fast8_t    pulse_1_len_min;                                         // minimum length of pulse with bit value 1
    uint_fast8_t    pulse_1_len_max;                                         // maximum length of pulse with bit value 1
    uint_fast8_t    pause_1_len_min;                                         // minimum length of pause with bit value 1
    uint_fast8_t    pause_1_len_max;                                         // maximum length of pause with bit value 1
    uint_fast8_t    pulse_0_len_min;                                         // minimum length of pulse with bit value 0
    uint_fast8_t    pulse_0_len_max;                                         // maximum length of pulse with bit value 0
    uint_fast8_t    pause_0_len_min;                                         // minimum length of pause with bit value 0
    uint_fast8_t    pause_0_len_max;                                         // maximum length of pause with bit value 0
    uint_fast8_t    address_offset;                                          // address offset
    uint_fast8_t    address_end;                                             // end of address
    uint_fast8_t    command_offset;                                          // command offset
    uint_fast8_t    command_end;                                             // end of command
    uint_fast8_t    complete_len;                                            // complete length of frame
    uint_fast8_t    stop_bit;                                                // flag: frame has stop bit
    uint_fast8_t    lsb_first;                                               // flag: LSB first
    uint_fast8_t    flags;                                                   // some flags
} IRMP_PARAMETER;

#if IRMP_SUPPORT_SIRCS_PROTOCOL == 1

static const PROGMEM IRMP_PARAMETER sircs_param =
{
    IRMP_SIRCS_PROTOCOL,                                                // protocol:        ir protocol
    SIRCS_1_PULSE_LEN_MIN,                                              // pulse_1_len_min: minimum length of pulse with bit value 1
    SIRCS_1_PULSE_LEN_MAX,                                              // pulse_1_len_max: maximum length of pulse with bit value 1
    SIRCS_PAUSE_LEN_MIN,                                                // pause_1_len_min: minimum length of pause with bit value 1
    SIRCS_PAUSE_LEN_MAX,                                                // pause_1_len_max: maximum length of pause with bit value 1
    SIRCS_0_PULSE_LEN_MIN,                                              // pulse_0_len_min: minimum length of pulse with bit value 0
    SIRCS_0_PULSE_LEN_MAX,                                              // pulse_0_len_max: maximum length of pulse with bit value 0
    SIRCS_PAUSE_LEN_MIN,                                                // pause_0_len_min: minimum length of pause with bit value 0
    SIRCS_PAUSE_LEN_MAX,                                                // pause_0_len_max: maximum length of pause with bit value 0
    SIRCS_ADDRESS_OFFSET,                                               // address_offset:  address offset
    SIRCS_ADDRESS_OFFSET + SIRCS_ADDRESS_LEN,                           // address_end:     end of address
    SIRCS_COMMAND_OFFSET,                                               // command_offset:  command offset
    SIRCS_COMMAND_OFFSET + SIRCS_COMMAND_LEN,                           // command_end:     end of command
    SIRCS_COMPLETE_DATA_LEN,                                            // complete_len:    complete length of frame
    SIRCS_STOP_BIT,                                                     // stop_bit:        flag: frame has stop bit
    SIRCS_LSB,                                                          // lsb_first:       flag: LSB first
    SIRCS_FLAGS                                                         // flags:           some flags
};

#endif

#if IRMP_SUPPORT_NEC_PROTOCOL == 1

static const PROGMEM IRMP_PARAMETER nec_param =
{
    IRMP_NEC_PROTOCOL,                                                  // protocol:        ir protocol
    NEC_PULSE_LEN_MIN,                                                  // pulse_1_len_min: minimum length of pulse with bit value 1
    NEC_PULSE_LEN_MAX,                                                  // pulse_1_len_max: maximum length of pulse with bit value 1
    NEC_1_PAUSE_LEN_MIN,                                                // pause_1_len_min: minimum length of pause with bit value 1
    NEC_1_PAUSE_LEN_MAX,                                                // pause_1_len_max: maximum length of pause with bit value 1
    NEC_PULSE_LEN_MIN,                                                  // pulse_0_len_min: minimum length of pulse with bit value 0
    NEC_PULSE_LEN_MAX,                                                  // pulse_0_len_max: maximum length of pulse with bit value 0
    NEC_0_PAUSE_LEN_MIN,                                                // pause_0_len_min: minimum length of pause with bit value 0
    NEC_0_PAUSE_LEN_MAX,                                                // pause_0_len_max: maximum length of pause with bit value 0
    NEC_ADDRESS_OFFSET,                                                 // address_offset:  address offset
    NEC_ADDRESS_OFFSET + NEC_ADDRESS_LEN,                               // address_end:     end of address
    NEC_COMMAND_OFFSET,                                                 // command_offset:  command offset
    NEC_COMMAND_OFFSET + NEC_COMMAND_LEN,                               // command_end:     end of command
    NEC_COMPLETE_DATA_LEN,                                              // complete_len:    complete length of frame
    NEC_STOP_BIT,                                                       // stop_bit:        flag: frame has stop bit
    NEC_LSB,                                                            // lsb_first:       flag: LSB first
    NEC_FLAGS                                                           // flags:           some flags
};

static const PROGMEM IRMP_PARAMETER nec_rep_param =
{
    IRMP_NEC_PROTOCOL,                                                  // protocol:        ir protocol
    NEC_PULSE_LEN_MIN,                                                  // pulse_1_len_min: minimum length of pulse with bit value 1
    NEC_PULSE_LEN_MAX,                                                  // pulse_1_len_max: maximum length of pulse with bit value 1
    NEC_1_PAUSE_LEN_MIN,                                                // pause_1_len_min: minimum length of pause with bit value 1
    NEC_1_PAUSE_LEN_MAX,                                                // pause_1_len_max: maximum length of pause with bit value 1
    NEC_PULSE_LEN_MIN,                                                  // pulse_0_len_min: minimum length of pulse with bit value 0
    NEC_PULSE_LEN_MAX,                                                  // pulse_0_len_max: maximum length of pulse with bit value 0
    NEC_0_PAUSE_LEN_MIN,                                                // pause_0_len_min: minimum length of pause with bit value 0
    NEC_0_PAUSE_LEN_MAX,                                                // pause_0_len_max: maximum length of pause with bit value 0
    0,                                                                  // address_offset:  address offset
    0,                                                                  // address_end:     end of address
    0,                                                                  // command_offset:  command offset
    0,                                                                  // command_end:     end of command
    0,                                                                  // complete_len:    complete length of frame
    NEC_STOP_BIT,                                                       // stop_bit:        flag: frame has stop bit
    NEC_LSB,                                                            // lsb_first:       flag: LSB first
    NEC_FLAGS                                                           // flags:           some flags
};

#endif

#if IRMP_SUPPORT_NEC42_PROTOCOL == 1

static const PROGMEM IRMP_PARAMETER nec42_param =
{
    IRMP_NEC42_PROTOCOL,                                                // protocol:        ir protocol
    NEC_PULSE_LEN_MIN,                                                  // pulse_1_len_min: minimum length of pulse with bit value 1
    NEC_PULSE_LEN_MAX,                                                  // pulse_1_len_max: maximum length of pulse with bit value 1
    NEC_1_PAUSE_LEN_MIN,                                                // pause_1_len_min: minimum length of pause with bit value 1
    NEC_1_PAUSE_LEN_MAX,                                                // pause_1_len_max: maximum length of pause with bit value 1
    NEC_PULSE_LEN_MIN,                                                  // pulse_0_len_min: minimum length of pulse with bit value 0
    NEC_PULSE_LEN_MAX,                                                  // pulse_0_len_max: maximum length of pulse with bit value 0
    NEC_0_PAUSE_LEN_MIN,                                                // pause_0_len_min: minimum length of pause with bit value 0
    NEC_0_PAUSE_LEN_MAX,                                                // pause_0_len_max: maximum length of pause with bit value 0
    NEC42_ADDRESS_OFFSET,                                               // address_offset:  address offset
    NEC42_ADDRESS_OFFSET + NEC42_ADDRESS_LEN,                           // address_end:     end of address
    NEC42_COMMAND_OFFSET,                                               // command_offset:  command offset
    NEC42_COMMAND_OFFSET + NEC42_COMMAND_LEN,                           // command_end:     end of command
    NEC42_COMPLETE_DATA_LEN,                                            // complete_len:    complete length of frame
    NEC_STOP_BIT,                                                       // stop_bit:        flag: frame has stop bit
    NEC_LSB,                                                            // lsb_first:       flag: LSB first
    NEC_FLAGS                                                           // flags:           some flags
};

#endif

#if IRMP_SUPPORT_LGAIR_PROTOCOL == 1
#if 0 // not needed, switching from NEC

static const PROGMEM IRMP_PARAMETER lgair_param =
{
    IRMP_LGAIR_PROTOCOL,                                                // protocol:        ir protocol
    NEC_PULSE_LEN_MIN,                                                  // pulse_1_len_min: minimum length of pulse with bit value 1
    NEC_PULSE_LEN_MAX,                                                  // pulse_1_len_max: maximum length of pulse with bit value 1
    NEC_1_PAUSE_LEN_MIN,                                                // pause_1_len_min: minimum length of pause with bit value 1
    NEC_1_PAUSE_LEN_MAX,                                                // pause_1_len_max: maximum length of pause with bit value 1
    NEC_PULSE_LEN_MIN,                                                  // pulse_0_len_min: minimum length of pulse with bit value 0
    NEC_PULSE_LEN_MAX,                                                  // pulse_0_len_max: maximum length of pulse with bit value 0
    NEC_0_PAUSE_LEN_MIN,                                                // pause_0_len_min: minimum length of pause with bit value 0
    NEC_0_PAUSE_LEN_MAX,                                                // pause_0_len_max: maximum length of pause with bit value 0
    LGAIR_ADDRESS_OFFSET,                                               // address_offset:  address offset
    LGAIR_ADDRESS_OFFSET + LGAIR_ADDRESS_LEN,                           // address_end:     end of address
    LGAIR_COMMAND_OFFSET,                                               // command_offset:  command offset
    LGAIR_COMMAND_OFFSET + LGAIR_COMMAND_LEN,                           // command_end:     end of command
    LGAIR_COMPLETE_DATA_LEN,                                            // complete_len:    complete length of frame
    NEC_STOP_BIT,                                                       // stop_bit:        flag: frame has stop bit
    NEC_LSB,                                                            // lsb_first:       flag: LSB first
    NEC_FLAGS                                                           // flags:           some flags
};

#endif // 0 not needed, switching from NEC
#endif

#if IRMP_SUPPORT_SAMSUNG_PROTOCOL == 1

static const PROGMEM IRMP_PARAMETER samsung_param =
{
    IRMP_SAMSUNG_PROTOCOL,                                              // protocol:        ir protocol
    SAMSUNG_PULSE_LEN_MIN,                                              // pulse_1_len_min: minimum length of pulse with bit value 1
    SAMSUNG_PULSE_LEN_MAX,                                              // pulse_1_len_max: maximum length of pulse with bit value 1
    SAMSUNG_1_PAUSE_LEN_MIN,                                            // pause_1_len_min: minimum length of pause with bit value 1
    SAMSUNG_1_PAUSE_LEN_MAX,                                            // pause_1_len_max: maximum length of pause with bit value 1
    SAMSUNG_PULSE_LEN_MIN,                                              // pulse_0_len_min: minimum length of pulse with bit value 0
    SAMSUNG_PULSE_LEN_MAX,                                              // pulse_0_len_max: maximum length of pulse with bit value 0
    SAMSUNG_0_PAUSE_LEN_MIN,                                            // pause_0_len_min: minimum length of pause with bit value 0
    SAMSUNG_0_PAUSE_LEN_MAX,                                            // pause_0_len_max: maximum length of pause with bit value 0
    SAMSUNG_ADDRESS_OFFSET,                                             // address_offset:  address offset
    SAMSUNG_ADDRESS_OFFSET + SAMSUNG_ADDRESS_LEN,                       // address_end:     end of address
    SAMSUNG_COMMAND_OFFSET,                                             // command_offset:  command offset
    SAMSUNG_COMMAND_OFFSET + SAMSUNG_COMMAND_LEN,                       // command_end:     end of command
    SAMSUNG_COMPLETE_DATA_LEN,                                          // complete_len:    complete length of frame
    SAMSUNG_STOP_BIT,                                                   // stop_bit:        flag: frame has stop bit
    SAMSUNG_LSB,                                                        // lsb_first:       flag: LSB first
    SAMSUNG_FLAGS                                                       // flags:           some flags
};

#endif

#if IRMP_SUPPORT_SAMSUNGAH_PROTOCOL == 1

static const PROGMEM IRMP_PARAMETER samsungah_param =
{
    IRMP_SAMSUNGAH_PROTOCOL,                                            // protocol:        ir protocol
    SAMSUNGAH_PULSE_LEN_MIN,                                            // pulse_1_len_min: minimum length of pulse with bit value 1
    SAMSUNGAH_PULSE_LEN_MAX,                                            // pulse_1_len_max: maximum length of pulse with bit value 1
    SAMSUNGAH_1_PAUSE_LEN_MIN,                                          // pause_1_len_min: minimum length of pause with bit value 1
    SAMSUNGAH_1_PAUSE_LEN_MAX,                                          // pause_1_len_max: maximum length of pause with bit value 1
    SAMSUNGAH_PULSE_LEN_MIN,                                            // pulse_0_len_min: minimum length of pulse with bit value 0
    SAMSUNGAH_PULSE_LEN_MAX,                                            // pulse_0_len_max: maximum length of pulse with bit value 0
    SAMSUNGAH_0_PAUSE_LEN_MIN,                                          // pause_0_len_min: minimum length of pause with bit value 0
    SAMSUNGAH_0_PAUSE_LEN_MAX,                                          // pause_0_len_max: maximum length of pause with bit value 0
    SAMSUNGAH_ADDRESS_OFFSET,                                           // address_offset:  address offset
    SAMSUNGAH_ADDRESS_OFFSET + SAMSUNGAH_ADDRESS_LEN,                   // address_end:     end of address
    SAMSUNGAH_COMMAND_OFFSET,                                           // command_offset:  command offset
    SAMSUNGAH_COMMAND_OFFSET + SAMSUNGAH_COMMAND_LEN,                   // command_end:     end of command
    SAMSUNGAH_COMPLETE_DATA_LEN,                                        // complete_len:    complete length of frame
    SAMSUNGAH_STOP_BIT,                                                 // stop_bit:        flag: frame has stop bit
    SAMSUNGAH_LSB,                                                      // lsb_first:       flag: LSB first
    SAMSUNGAH_FLAGS                                                     // flags:           some flags
};

#endif

#if IRMP_SUPPORT_TELEFUNKEN_PROTOCOL == 1

static const PROGMEM IRMP_PARAMETER telefunken_param =
{
    IRMP_TELEFUNKEN_PROTOCOL,                                           // protocol:        ir protocol
    TELEFUNKEN_PULSE_LEN_MIN,                                           // pulse_1_len_min: minimum length of pulse with bit value 1
    TELEFUNKEN_PULSE_LEN_MAX,                                           // pulse_1_len_max: maximum length of pulse with bit value 1
    TELEFUNKEN_1_PAUSE_LEN_MIN,                                         // pause_1_len_min: minimum length of pause with bit value 1
    TELEFUNKEN_1_PAUSE_LEN_MAX,                                         // pause_1_len_max: maximum length of pause with bit value 1
    TELEFUNKEN_PULSE_LEN_MIN,                                           // pulse_0_len_min: minimum length of pulse with bit value 0
    TELEFUNKEN_PULSE_LEN_MAX,                                           // pulse_0_len_max: maximum length of pulse with bit value 0
    TELEFUNKEN_0_PAUSE_LEN_MIN,                                         // pause_0_len_min: minimum length of pause with bit value 0
    TELEFUNKEN_0_PAUSE_LEN_MAX,                                         // pause_0_len_max: maximum length of pause with bit value 0
    TELEFUNKEN_ADDRESS_OFFSET,                                          // address_offset:  address offset
    TELEFUNKEN_ADDRESS_OFFSET + TELEFUNKEN_ADDRESS_LEN,                 // address_end:     end of address
    TELEFUNKEN_COMMAND_OFFSET,                                          // command_offset:  command offset
    TELEFUNKEN_COMMAND_OFFSET + TELEFUNKEN_COMMAND_LEN,                 // command_end:     end of command
    TELEFUNKEN_COMPLETE_DATA_LEN,                                       // complete_len:    complete length of frame
    TELEFUNKEN_STOP_BIT,                                                // stop_bit:        flag: frame has stop bit
    TELEFUNKEN_LSB,                                                     // lsb_first:       flag: LSB first
    TELEFUNKEN_FLAGS                                                    // flags:           some flags
};

#endif

#if IRMP_SUPPORT_MATSUSHITA_PROTOCOL == 1

static const PROGMEM IRMP_PARAMETER matsushita_param =
{
    IRMP_MATSUSHITA_PROTOCOL,                                           // protocol:        ir protocol
    MATSUSHITA_PULSE_LEN_MIN,                                           // pulse_1_len_min: minimum length of pulse with bit value 1
    MATSUSHITA_PULSE_LEN_MAX,                                           // pulse_1_len_max: maximum length of pulse with bit value 1
    MATSUSHITA_1_PAUSE_LEN_MIN,                                         // pause_1_len_min: minimum length of pause with bit value 1
    MATSUSHITA_1_PAUSE_LEN_MAX,                                         // pause_1_len_max: maximum length of pause with bit value 1
    MATSUSHITA_PULSE_LEN_MIN,                                           // pulse_0_len_min: minimum length of pulse with bit value 0
    MATSUSHITA_PULSE_LEN_MAX,                                           // pulse_0_len_max: maximum length of pulse with bit value 0
    MATSUSHITA_0_PAUSE_LEN_MIN,                                         // pause_0_len_min: minimum length of pause with bit value 0
    MATSUSHITA_0_PAUSE_LEN_MAX,                                         // pause_0_len_max: maximum length of pause with bit value 0
    MATSUSHITA_ADDRESS_OFFSET,                                          // address_offset:  address offset
    MATSUSHITA_ADDRESS_OFFSET + MATSUSHITA_ADDRESS_LEN,                 // address_end:     end of address
    MATSUSHITA_COMMAND_OFFSET,                                          // command_offset:  command offset
    MATSUSHITA_COMMAND_OFFSET + MATSUSHITA_COMMAND_LEN,                 // command_end:     end of command
    MATSUSHITA_COMPLETE_DATA_LEN,                                       // complete_len:    complete length of frame
    MATSUSHITA_STOP_BIT,                                                // stop_bit:        flag: frame has stop bit
    MATSUSHITA_LSB,                                                     // lsb_first:       flag: LSB first
    MATSUSHITA_FLAGS                                                    // flags:           some flags
};

#endif

#if IRMP_SUPPORT_KASEIKYO_PROTOCOL == 1

static const PROGMEM IRMP_PARAMETER kaseikyo_param =
{
    IRMP_KASEIKYO_PROTOCOL,                                             // protocol:        ir protocol
    KASEIKYO_PULSE_LEN_MIN,                                             // pulse_1_len_min: minimum length of pulse with bit value 1
    KASEIKYO_PULSE_LEN_MAX,                                             // pulse_1_len_max: maximum length of pulse with bit value 1
    KASEIKYO_1_PAUSE_LEN_MIN,                                           // pause_1_len_min: minimum length of pause with bit value 1
    KASEIKYO_1_PAUSE_LEN_MAX,                                           // pause_1_len_max: maximum length of pause with bit value 1
    KASEIKYO_PULSE_LEN_MIN,                                             // pulse_0_len_min: minimum length of pulse with bit value 0
    KASEIKYO_PULSE_LEN_MAX,                                             // pulse_0_len_max: maximum length of pulse with bit value 0
    KASEIKYO_0_PAUSE_LEN_MIN,                                           // pause_0_len_min: minimum length of pause with bit value 0
    KASEIKYO_0_PAUSE_LEN_MAX,                                           // pause_0_len_max: maximum length of pause with bit value 0
    KASEIKYO_ADDRESS_OFFSET,                                            // address_offset:  address offset
    KASEIKYO_ADDRESS_OFFSET + KASEIKYO_ADDRESS_LEN,                     // address_end:     end of address
    KASEIKYO_COMMAND_OFFSET,                                            // command_offset:  command offset
    KASEIKYO_COMMAND_OFFSET + KASEIKYO_COMMAND_LEN,                     // command_end:     end of command
    KASEIKYO_COMPLETE_DATA_LEN,                                         // complete_len:    complete length of frame
    KASEIKYO_STOP_BIT,                                                  // stop_bit:        flag: frame has stop bit
    KASEIKYO_LSB,                                                       // lsb_first:       flag: LSB first
    KASEIKYO_FLAGS                                                      // flags:           some flags
};

#endif

#if IRMP_SUPPORT_PANASONIC_PROTOCOL == 1

static const PROGMEM IRMP_PARAMETER panasonic_param =
{
    IRMP_PANASONIC_PROTOCOL,                                            // protocol:        ir protocol
    PANASONIC_PULSE_LEN_MIN,                                            // pulse_1_len_min: minimum length of pulse with bit value 1
    PANASONIC_PULSE_LEN_MAX,                                            // pulse_1_len_max: maximum length of pulse with bit value 1
    PANASONIC_1_PAUSE_LEN_MIN,                                          // pause_1_len_min: minimum length of pause with bit value 1
    PANASONIC_1_PAUSE_LEN_MAX,                                          // pause_1_len_max: maximum length of pause with bit value 1
    PANASONIC_PULSE_LEN_MIN,                                            // pulse_0_len_min: minimum length of pulse with bit value 0
    PANASONIC_PULSE_LEN_MAX,                                            // pulse_0_len_max: maximum length of pulse with bit value 0
    PANASONIC_0_PAUSE_LEN_MIN,                                          // pause_0_len_min: minimum length of pause with bit value 0
    PANASONIC_0_PAUSE_LEN_MAX,                                          // pause_0_len_max: maximum length of pause with bit value 0
    PANASONIC_ADDRESS_OFFSET,                                           // address_offset:  address offset
    PANASONIC_ADDRESS_OFFSET + PANASONIC_ADDRESS_LEN,                   // address_end:     end of address
    PANASONIC_COMMAND_OFFSET,                                           // command_offset:  command offset
    PANASONIC_COMMAND_OFFSET + PANASONIC_COMMAND_LEN,                   // command_end:     end of command
    PANASONIC_COMPLETE_DATA_LEN,                                        // complete_len:    complete length of frame
    PANASONIC_STOP_BIT,                                                 // stop_bit:        flag: frame has stop bit
    PANASONIC_LSB,                                                      // lsb_first:       flag: LSB first
    PANASONIC_FLAGS                                                     // flags:           some flags
};

#endif

#if IRMP_SUPPORT_MITSU_HEAVY_PROTOCOL == 1

static const PROGMEM IRMP_PARAMETER mitsu_heavy_param =
{
    IRMP_MITSU_HEAVY_PROTOCOL,                                          // protocol:        ir protocol
    MITSU_HEAVY_PULSE_LEN_MIN,                                          // pulse_1_len_min: minimum length of pulse with bit value 1
    MITSU_HEAVY_PULSE_LEN_MAX,                                          // pulse_1_len_max: maximum length of pulse with bit value 1
    MITSU_HEAVY_1_PAUSE_LEN_MIN,                                        // pause_1_len_min: minimum length of pause with bit value 1
    MITSU_HEAVY_1_PAUSE_LEN_MAX,                                        // pause_1_len_max: maximum length of pause with bit value 1
    MITSU_HEAVY_PULSE_LEN_MIN,                                          // pulse_0_len_min: minimum length of pulse with bit value 0
    MITSU_HEAVY_PULSE_LEN_MAX,                                          // pulse_0_len_max: maximum length of pulse with bit value 0
    MITSU_HEAVY_0_PAUSE_LEN_MIN,                                        // pause_0_len_min: minimum length of pause with bit value 0
    MITSU_HEAVY_0_PAUSE_LEN_MAX,                                        // pause_0_len_max: maximum length of pause with bit value 0
    MITSU_HEAVY_ADDRESS_OFFSET,                                         // address_offset:  address offset
    MITSU_HEAVY_ADDRESS_OFFSET + MITSU_HEAVY_ADDRESS_LEN,               // address_end:     end of address
    MITSU_HEAVY_COMMAND_OFFSET,                                         // command_offset:  command offset
    MITSU_HEAVY_COMMAND_OFFSET + MITSU_HEAVY_COMMAND_LEN,               // command_end:     end of command
    MITSU_HEAVY_COMPLETE_DATA_LEN,                                      // complete_len:    complete length of frame
    MITSU_HEAVY_STOP_BIT,                                               // stop_bit:        flag: frame has stop bit
    MITSU_HEAVY_LSB,                                                    // lsb_first:       flag: LSB first
    MITSU_HEAVY_FLAGS                                                   // flags:           some flags
};

#endif
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
