Solartraveler/UniversalboxArm/src/apps/09-gamebox/arm/userinput.c

/*
   Gamebox
    Copyright (C) 2004-2006  by Malte Marwedel
    m.talk AT marwedels dot de

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
    You should have received a copy of the GNU General Public License
    along with this program; if not, write to the Free Software
    Foundation, Inc., 59 Temple Place, Suite 330, Boston, MA  02111-1307  USA
*/

#include <stdbool.h>

#include "main.h"

#include "FreeRTOS.h"
#include "semphr.h"
#include "task.h"
#include "boxlib/keys.h"
#include "boxlib/keysIsr.h"
#include "boxlib/simpleadc.h"
#include "utility.h"
#include "filesystem.h"
#include "json.h"

#define JOYSTICK_FILENAME "/etc/joystick.json"
#define FILE_MAX 256

#define INPUT_PORT GPIOC
#define INPUT_KEY_PIN GPIO_PIN_3
#define INPUT_X_PIN GPIO_PIN_0
#define INPUT_X_ADC 1
#define INPUT_Y_PIN GPIO_PIN_1
#define INPUT_Y_ADC 2

#define INP_LINEARIZE 4095000
#define INP_SCALE 200
#define INP_LIM 127
#define INP_SNAP_IN 96
#define INP_SNAP_OUT 32



struct userinputstruct userin;
struct userinputcalibstruct calib_x;
struct userinputcalibstruct calib_y;

const char input_calib_text1[] PROGMEM = "All sides move, press key in center";
const char input_calib_text2[] PROGMEM = "Cali:";

SemaphoreHandle_t g_inputSemaphore;
StaticSemaphore_t g_inputSemaphoreState;

uint8_t g_userinputtype; //0 = Keys + joystick key for detection, 1 Joystick + keys, 2 = Keys only

void InputLock(void) {
	while (!xSemaphoreTake(g_inputSemaphore, 1000));
}

void InputUnlock(void) {
	xSemaphoreGive(g_inputSemaphore);
}

#if modul_calib_save

const char input_calib_save1[] PROGMEM = "Save joystick calib in file?";
const char input_calib_no[] PROGMEM = "No";
const char input_calib_yes[] PROGMEM = "Yes";
const char input_calib_save2[] PROGMEM = "Values saved";

void calib_load(void) {
	uint8_t jsonfile[FILE_MAX] = {0};
	size_t r = 0;
	char value[8];
	uint8_t num = 0;
	if (FilesystemReadFile(JOYSTICK_FILENAME, jsonfile, sizeof(jsonfile) - 1, &r)) {
		InputLock();
		if (JsonValueGet(jsonfile, r, "centerX1", value, sizeof(value))) {
			calib_x.zero = MAX(atoi(value), 1);
			num++;
		}
		if (JsonValueGet(jsonfile, r, "minX1", value, sizeof(value))) {
			calib_x.min = MAX(atoi(value), 1);
			num++;
		}
		if (JsonValueGet(jsonfile, r, "maxX1", value, sizeof(value))) {
			calib_x.max = MAX(atoi(value), 1);
			num++;
		}
		if (JsonValueGet(jsonfile, r, "center1", value, sizeof(value))) {
			calib_y.zero = MAX(atoi(value), 1);
			num++;
		}
		if (JsonValueGet(jsonfile, r, "minY1", value, sizeof(value))) {
			calib_y.min = MAX(atoi(value), 1);
			num++;
		}
		if (JsonValueGet(jsonfile, r, "maxY1", value, sizeof(value))) {
			calib_y.max = MAX(atoi(value), 1);
			num++;
		}
		InputUnlock();
		printf("%u calibration values loaded\r\n", num);
	}
}

void calib_save(void) {
	u08 accepted = 0;
	clear_screen();
	load_text(input_calib_save1);
	scrolltext(0, 0x03, 0, 120);
	load_text(input_calib_no);
	draw_string(1, 8, 0x31, 0, 1);
	while (userin_press() == 0) {
		if ((userin_right()) && (accepted == 0)) { //Yes
			accepted = 1;
			load_text(input_calib_yes);
			draw_box(0, 8, 16, 8, 0x00, 0x00);
		}
		if (userin_left() || userin_up() || userin_down()) { //No
			accepted = 0;
			load_text(input_calib_no);
			draw_box(0, 8, 16, 8, 0x00, 0x00);
		}
		draw_string(1, 8, 0x31, 0, 1);
	}
	if (accepted == 1) { //save to filesystem
		char buffer[FILE_MAX];
		snprintf(buffer, sizeof(buffer), "{\
		\n  \"centerX1\": \"%u\",\n  \"minX1\": \"%u\",\n  \"maxX1\": \"%u\",\n\
		  \"centerY1\": \"%u\",\n  \"minY1\": \"%u\",\n  \"maxY1\": \"%u\",\n}",
		         calib_x.zero, calib_x.min, calib_x.max,
		         calib_y.zero, calib_y.min, calib_y.max);
		if (FilesystemWriteEtcFile(JOYSTICK_FILENAME, buffer, strlen(buffer))) {
			printf("Saved to %s\r\n", JOYSTICK_FILENAME);
			load_text(input_calib_save2);
			scrolltext(3,0x13,0,120);
		} else {
			printf("Error, could not create file %s\r\n", JOYSTICK_FILENAME);
		}
		waitms(500);
		userin_flush();
	}
}

#endif

void input_calib(void) {
	uint16_t min_x = 4096, min_y = 4096;
	uint16_t max_x = 1, max_y = 1;
	uint16_t medium_x,medium_y;
	uint16_t temp;
	static uint8_t input_calib_ignoretext;

	if (input_calib_ignoretext == 0) {
		input_calib_ignoretext = 1;
		load_text(input_calib_text1);
		scrolltext(0, 0x03, 0, 100);
		waitms(250);
	}
	load_text(input_calib_text2);
	draw_box(0, 0, 16, 8, 0x00, 0x00); //clear the text
	draw_string(0, 0, 0x03, 0, 1);
	InputLock();
	while (HAL_GPIO_ReadPin(INPUT_PORT, INPUT_KEY_PIN) == GPIO_PIN_SET) {
		//Calib of X
		temp = AdcGet(INPUT_X_ADC);
		showbin(9, temp, 0x30);
		if (temp < min_x) {
			min_x = temp;
		}
		if (temp > max_x) {
			max_x = temp;
		}
		//Calib of Y
		temp = AdcGet(INPUT_Y_ADC);
		showbin(13, temp, 0x30);
		if (temp < min_y) {
			min_y = temp;
		}
		if (temp > max_y) {
			max_y = temp;
		}
		//Show as binary
		showbin(8 , min_x, 0x03);
		showbin(10, max_x, 0x03);
		showbin(12, min_y, 0x03);
		showbin(14, max_y, 0x03);
	}
	//Measure the centre
	medium_x = AdcGet(INPUT_X_ADC);
	medium_y = AdcGet(INPUT_Y_ADC);;
	//No value may be zero, as it will be used as divider
	if (min_x == 0) {
		min_x = 1;
	}
	if (min_y == 0) {
		min_y = 1;
	}
	if (medium_x == 0) {
		medium_x = 1;
	}
	if (medium_y == 0) {
		medium_y = 1;
	}
	//calc calibration values
	calib_x.zero = INP_LINEARIZE/medium_x;
	calib_y.zero = INP_LINEARIZE/medium_y;
	calib_x.max = (INP_LINEARIZE/max_x - calib_x.zero) *(-1); // *(-1) for positive value
	calib_y.max = (INP_LINEARIZE/max_y - calib_y.zero) *(-1);
	calib_x.min = INP_LINEARIZE/min_x - calib_x.zero;
	calib_y.min = INP_LINEARIZE/min_y - calib_y.zero;
	//Input thread should work again
	InputUnlock();
}

void input_select(void) {
	/* If key on joystick is pressed: userinputtype = 1;
	   If key up or down is pressed: userinputtype = 2;
	   If userin_right() -> go to main menu
	*/
	g_userinputtype = 0;
	userin_flush();
	load_text("Input?");
	scrolltext(0, 0x03, 0, 80);
	load_text("In?");
	draw_box(0, 0, 16, 8, 0x00, 0x00);
	draw_string(0, 0, 0x03, 0, 1);
	while (userin_right() == 0) {
		if (userin_press()) {
			g_userinputtype = 1;
			load_text("Joy");
			draw_box(0, 8, 16, 7, 0x00, 0x00);
			draw_string(0, 8, 0x13, 0, 1);
			waitms(100);
		}
		if ((KeyUpPressed()) || KeyDownPressed() || KeyLeftPressed()) {
			g_userinputtype = 2;
			load_text("Key");
			draw_box(0,8,16,7,0x00,0x00);
			draw_string(0,8,0x13,0,1);
			waitms(100);
		}
	}
}

void JoystickInit(void) {
	if (g_inputSemaphore == NULL) {
		g_inputSemaphore = xSemaphoreCreateMutexStatic(&g_inputSemaphoreState);
	}
	AdcInit();
	__HAL_RCC_GPIOC_CLK_ENABLE();
	//For the x and y axis
	GPIO_InitTypeDef GPIO_InitStruct = {0};
	GPIO_InitStruct.Pin = INPUT_X_PIN | INPUT_Y_PIN;
	GPIO_InitStruct.Mode = GPIO_MODE_ANALOG;
	GPIO_InitStruct.Pull = GPIO_NOPULL;
	GPIO_InitStruct.Speed = GPIO_SPEED_FREQ_LOW;
	HAL_GPIO_Init(INPUT_PORT, &GPIO_InitStruct);
	//for the button
	GPIO_InitStruct.Pin = INPUT_KEY_PIN;
	GPIO_InitStruct.Mode = GPIO_MODE_INPUT;
	GPIO_InitStruct.Pull = GPIO_PULLUP;
	GPIO_InitStruct.Speed = GPIO_SPEED_FREQ_LOW;
	HAL_GPIO_Init(INPUT_PORT, &GPIO_InitStruct);
	//some simple default values
	calib_x.min = 500;
	calib_x.zero = 1800;
	calib_x.max = 500;
	calib_y.min = 500;
	calib_y.zero = 1800;
	calib_y.max = 500;
	InputUnlock();
}

/*This simply assumes the function is called every 1ms
  (see sleep at end of InputThread + there is at least the game thread running
  every other 1ms) so timing is not exact.
  Scope analysis show the inputs are jittering within a
  timeframe of 50ms.

  This function only calculates the average value.
  A median value might even be a better filter.
*/
#define AVERAGE_NUM 50
#define AVERAGE_CHANNELS 2

uint16_t g_adcData[AVERAGE_CHANNELS][AVERAGE_NUM];
uint16_t g_adcIdx[AVERAGE_CHANNELS];
uint32_t g_adcSum[AVERAGE_CHANNELS];

uint16_t AdcAverager(uint8_t channel) {
	uint16_t channelIdx;
	if (channel == INPUT_X_ADC) {
		channelIdx = 0;
	} else if (channel == INPUT_Y_ADC) {
		channelIdx = 1;
	} else {
		return 0; //should not happen
	}
	uint16_t * adcDataHistory = g_adcData[channelIdx];
	uint16_t idx = g_adcIdx[channelIdx];
	uint32_t sum = g_adcSum[channelIdx];

	uint16_t adcData = AdcGet(channel);
	if (adcDataHistory[idx] < sum) {
		sum -= adcDataHistory[idx];
	}
	adcDataHistory[idx] = adcData;
	sum += adcData;
	idx++;
	if (idx >= AVERAGE_NUM) {
		idx = 0;
	}
	g_adcIdx[channelIdx] = idx;
	g_adcSum[channelIdx] = sum;
	//enable to get some statistics how often this function is called for one channel
#if 0
	static uint32_t cycle = 0;
	static uint32_t tStart;
	if ((idx == 0) && (channelIdx == 0)) {
		if (cycle == 0) {
			tStart = HAL_GetTick();
		} else if (cycle == 1) {
			uint32_t tStop = HAL_GetTick();
			printf("%u calls take %u ticks\r\n", AVERAGE_NUM, (unsigned int)(tStop - tStart));
		}
		if (cycle == 39) { //approx 1 message per second
			cycle = 0;
		} else {
			cycle++;
		}
	}
#endif
	return sum / AVERAGE_NUM;
}

void InputThread(void * param) {
	(void)param;
	uint8_t snapKey = 0, snapX = 0, snapY = 0;
	uint32_t timestampPressL = 0, timestampPressR = 0;
	uint32_t timestampPressU = 0, timestampPressD = 0;
	while(1) {
		InputLock();
		if ((g_userinputtype == 0) || (g_userinputtype == 1)) {
			if (HAL_GPIO_ReadPin(INPUT_PORT, INPUT_KEY_PIN) == GPIO_PIN_RESET) {
				if (snapKey == 0) {
					userin.press = 1;
					snapKey = 1;
				}
			} else {
				snapKey = 0;
			}
		}
		if (g_userinputtype == 1) { //joystick input
			uint16_t x = AdcAverager(INPUT_X_ADC);
			int16_t xLin = 0;
			if (x) {
				xLin = (INP_LINEARIZE / x); //make linear
				xLin -= calib_x.zero;
				if (xLin < 0) {
					xLin = xLin * INP_SCALE / calib_x.min;
				} else if (xLin > 0) {
					xLin = xLin * INP_SCALE / calib_x.max;
				}
				xLin = MAX(-INP_LIM, MIN(INP_LIM, xLin));
				userin.x = xLin;
			}
			if ((xLin > INP_SNAP_IN) && (snapX == 0)) {
				snapX = 1;
				userin.right = 1;
			}
			if ((xLin < -INP_SNAP_IN) && (snapX == 0)) {
				snapX = 1;
				userin.left = 1;
			}
			if ((xLin < INP_SNAP_OUT) && (xLin > -INP_SNAP_OUT)) {
				snapX = 0;
			}

			uint16_t y = AdcAverager(INPUT_Y_ADC);
			int16_t yLin = 0;
			if (y) {
				yLin = (INP_LINEARIZE / y); //make linear
				yLin -= calib_y.zero;
				if (xLin < 0) {
					yLin = yLin * INP_SCALE / calib_y.min;
				} else if (xLin > 0) {
					yLin = yLin * INP_SCALE / calib_y.max;
				}
				yLin = MAX(-INP_LIM, MIN(INP_LIM, yLin));
			}
			userin.y = yLin;
			if ((yLin > INP_SNAP_IN) && (snapY == 0)) {
				snapY = 1;
				userin.down = 1;
			}
			if ((yLin < -INP_SNAP_IN) && (snapY == 0)) {
				snapY = 1;
				userin.up = 1;
			}
			if ((yLin < INP_SNAP_OUT) && (yLin > -INP_SNAP_OUT)) {
				snapY = 0;
			}
		}
		InputUnlock();
		//printf("X: %u -> %i, Y: %u -> %i\r\n", x,userin.x, y, userin.y);
		//If the keypad instead of the joystick is used
		/* The problem: There is a 5th key as joystick button replacement missing.
		   So up + down is used instead and all games try to avoid the need for the
		   joystick button if possible, if the keypad is used.
		*/
		if ((KeyUpPressed()) && (KeyDownPressed())) {
			userin.press = 1;
			timestampPressL = 0;
			timestampPressR = 0;
			timestampPressU = 0;
			timestampPressD = 0;
			userin.x = 0;
			userin.y = 0;
		} else {
			uint32_t timestamp = HAL_GetTick();
			const uint32_t minTime = 100; //time where the user has to hold the key without pressing a second one
			const uint32_t addTime = 200; //time until a second press is registered
			if (KeyLeftPressed()) {
				userin.right = 0;
				userin.up = 0;
				userin.down = 0;
				if (timestampPressL == 0) {
					timestampPressL = timestamp + minTime;
				} else if (timestampPressL < timestamp) {
					userin.left = 1;
					userin.x = -INP_LIM;
					timestampPressL += addTime; //wait until a second press
				}
			} else {
				timestampPressL = 0;
			}
			if (KeyRightPressed()) {
				userin.left = 0;
				userin.up = 0;
				userin.down = 0;
				if (timestampPressR == 0) {
					timestampPressR = timestamp + minTime;
				} else if (timestampPressR < timestamp) {
					userin.right = 1;
					userin.x = INP_LIM;
					timestampPressR += addTime; //wait until a second press
				}
			} else {
				timestampPressR = 0;
			}
			if ((g_userinputtype == 2) && (KeyLeftPressed() == 0) && (KeyRightPressed() == 0)) {
				userin.x = 0;
			}
			if (KeyUpPressed()) {
				userin.left = 0;
				userin.right = 0;
				userin.down = 0;
				if (timestampPressU == 0) {
					timestampPressU = timestamp + minTime;
				} else if (timestampPressU < timestamp) {
					userin.up = 1;
					userin.y = -INP_LIM;
					timestampPressU += addTime; //wait until a second press
				}
			} else {
				timestampPressU = 0;
			}
			if (KeyDownPressed()) {
				userin.left = 0;
				userin.right = 0;
				userin.up = 0;
				if (timestampPressD == 0) {
					timestampPressD = timestamp + minTime;
				} else if (timestampPressD < timestamp) {
					userin.down = 1;
					userin.y = INP_LIM;
					timestampPressD += addTime; //wait until a second press
				}
			} else {
				timestampPressD = 0;
			}
			if ((g_userinputtype == 2) && (KeyUpPressed() == 0) && (KeyDownPressed() == 0)) {
				userin.y = 0;
			}
		}
		vTaskDelay(1);
	}
}

void InputDebug(char c) {
	/* Yes, this results in a long wait while calibration is ongoing
	   and there the watchdog might get triggered.
	*/
	InputLock();
	if (c == 'w') {
		userin.up = 1;
		userin.y = -INP_LIM;
		vTaskDelay(100);
		userin.y = 0;
	}
	if (c == 'a') {
		userin.left = 1;
		userin.x = -INP_LIM;
		vTaskDelay(100);
		userin.x = 0;
	}
	if (c == 's') {
		userin.down = 1;
		userin.y = INP_LIM;
		vTaskDelay(100);
		userin.y = 0;
	}
	if (c == 'd') {
		userin.right = 1;
		userin.x = INP_LIM;
		vTaskDelay(100);
		userin.x = 0;
	}
	if (c == ' ') {
		userin.press = 1;
	}
	InputUnlock();
}

void reduceCPU(void) {
	vTaskDelay(1);
}

u08 userin_usekeys(void) {
	if (g_userinputtype == 2) {
		return 1;
	}
	return 0;
}

u08 userin_left(void) {
	reduceCPU();
	if (userin.left) {
		userin.left = 0;
		return 1;
	}
	return 0;
}

u08 userin_right(void) {
	reduceCPU();
	if (userin.right) {
		userin.right = 0;
		return 1;
	}
	return 0;
}

u08 userin_up(void) {
	reduceCPU();
	if (userin.up) {
		userin.up = 0;
		return 1;
	}
	return 0;
}

u08 userin_down(void) {
	reduceCPU();
	if (userin.down) {
		userin.down = 0;
		return 1;
	}
	return 0;
}

u08 userin_press(void) {
	reduceCPU();
	if (userin.press) {
		userin.press = 0;
		return 1;
	}
	return 0;
}

void userin_flush(void) {
	userin.left = 0;
	userin.right = 0;
	userin.up = 0;
	userin.down = 0;
	userin.press = 0;
}
