Solartraveler/UniversalboxArm/src/common/libmad/mad.h

/*
 * libmad - MPEG audio decoder library
 * Copyright (C) 2000-2004 Underbit Technologies, Inc.
 *
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
 * If you would like to negotiate alternate licensing terms, you may do
 * so by contacting: Underbit Technologies, Inc. <info@underbit.com>
 */

# ifdef __cplusplus
extern "C" {
# endif

/* #undef FPM_INTEL */
/* #undef FPM_ARM */
/* #undef FPM_MIPS */
/* #undef FPM_SPARC */
/* #undef FPM_PPC */
/* #undef FPM_64BIT */
/* #undef FPM_DEFAULT */

# define SIZEOF_INT 4

/* Id: version.h,v 1.26 2004/01/23 09:41:33 rob Exp */

# ifndef LIBMAD_VERSION_H
# define LIBMAD_VERSION_H

# define MAD_VERSION_MAJOR	0
# define MAD_VERSION_MINOR	16
# define MAD_VERSION_PATCH	4
# define MAD_VERSION_EXTRA	""

# define MAD_VERSION_STRINGIZE(str)	#str
# define MAD_VERSION_STRING(num)	MAD_VERSION_STRINGIZE(num)

# define MAD_VERSION		MAD_VERSION_STRING(MAD_VERSION_MAJOR) "."  \
				MAD_VERSION_STRING(MAD_VERSION_MINOR) "."  \
				MAD_VERSION_STRING(MAD_VERSION_PATCH)  \
				MAD_VERSION_EXTRA

# define MAD_PUBLISHYEAR	"2000-2004"
# define MAD_AUTHOR		"Underbit Technologies, Inc."
# define MAD_EMAIL		"info@underbit.com"

extern char const mad_version[];
extern char const mad_copyright[];
extern char const mad_author[];
extern char const mad_build[];

# endif

/* Id: fixed.h,v 1.38 2004/02/17 02:02:03 rob Exp */

# ifndef LIBMAD_FIXED_H
# define LIBMAD_FIXED_H

# include <stdint.h>

# if SIZEOF_INT >= 4
typedef   signed int mad_fixed_t;
typedef   signed int mad_fixed64hi_t;
typedef unsigned int mad_fixed64lo_t;
# else
typedef   signed long mad_fixed_t;
typedef   signed long mad_fixed64hi_t;
typedef unsigned long mad_fixed64lo_t;
# endif

typedef int64_t mad_fixed64_t;

# if defined(FPM_FLOAT)
typedef double mad_sample_t;
# else
typedef mad_fixed_t mad_sample_t;
# endif

/*
 * Fixed-point format: 0xABBBBBBB
 * A == whole part      (sign + 3 bits)
 * B == fractional part (28 bits)
 *
 * Values are signed two's complement, so the effective range is:
 * 0x80000000 to 0x7fffffff
 *       -8.0 to +7.9999999962747097015380859375
 *
 * The smallest representable value is:
 * 0x00000001 == 0.0000000037252902984619140625 (i.e. about 3.725e-9)
 *
 * 28 bits of fractional accuracy represent about
 * 8.6 digits of decimal accuracy.
 *
 * Fixed-point numbers can be added or subtracted as normal
 * integers, but multiplication requires shifting the 64-bit result
 * from 56 fractional bits back to 28 (and rounding.)
 *
 * Changing the definition of MAD_F_FRACBITS is only partially
 * supported, and must be done with care.
 */

# define MAD_F_FRACBITS		28

# if MAD_F_FRACBITS == 28
#  define MAD_F(x)		((mad_fixed_t) (x##L))
# else
#  if MAD_F_FRACBITS < 28
#   warning "MAD_F_FRACBITS < 28"
#   define MAD_F(x)		((mad_fixed_t)  \
				 (((x##L) +  \
				   (1L << (28 - MAD_F_FRACBITS - 1))) >>  \
				  (28 - MAD_F_FRACBITS)))
#  elif MAD_F_FRACBITS > 28
#   error "MAD_F_FRACBITS > 28 not currently supported"
#   define MAD_F(x)		((mad_fixed_t)  \
				 ((x##L) << (MAD_F_FRACBITS - 28)))
#  endif
# endif

# define MAD_F_MIN		((mad_fixed_t) -0x80000000L)
# define MAD_F_MAX		((mad_fixed_t) +0x7fffffffL)

# define MAD_F_ONE		MAD_F(0x10000000)

# define mad_f_tofixed(x)	((mad_fixed_t)  \
				 ((x) * (double) (1L << MAD_F_FRACBITS) + 0.5))
# define mad_f_todouble(x)	((double)  \
				 ((x) / (double) (1L << MAD_F_FRACBITS)))

# define mad_f_intpart(x)	((x) >> MAD_F_FRACBITS)
# define mad_f_fracpart(x)	((x) & ((1L << MAD_F_FRACBITS) - 1))
				/* (x should be positive) */

# define mad_f_fromint(x)	((x) << MAD_F_FRACBITS)
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
